swyou1123/ssokdam/Docs/ERD.png

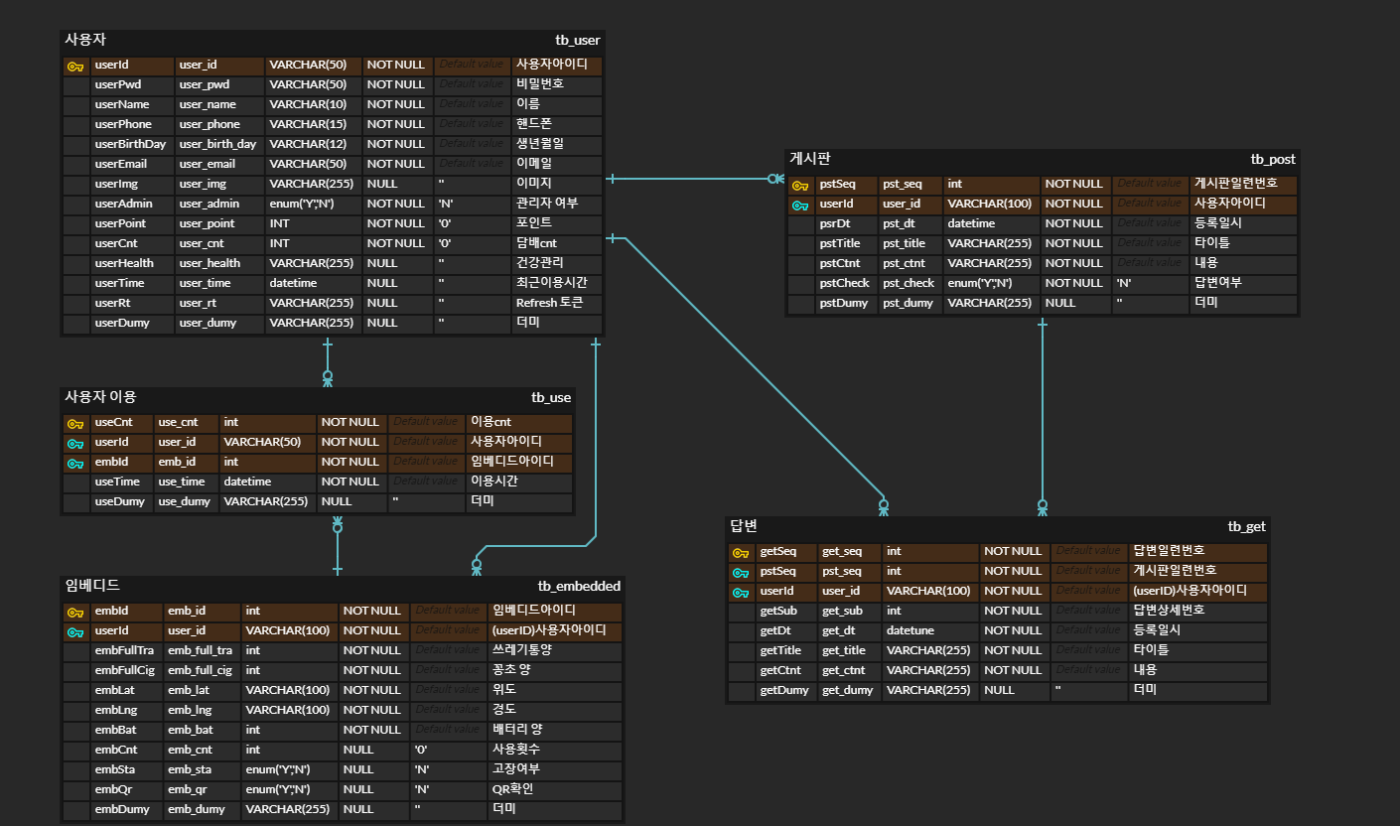
Docs/ERD.png
