swyou1123/ssokdam/Embedded/ESP32s/Sensor/AirQuality_Sensor/Reference/Check.png

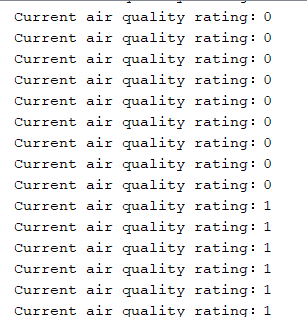
Embedded/ESP32s/Sensor/AirQuality_Sensor/Reference/Check.png
