swyou1123/ssokdam/Embedded/ESP32s/Sensor/Contactfree_Temp_Sensor/Reference/비접촉온도센서 테스트(arduino).png

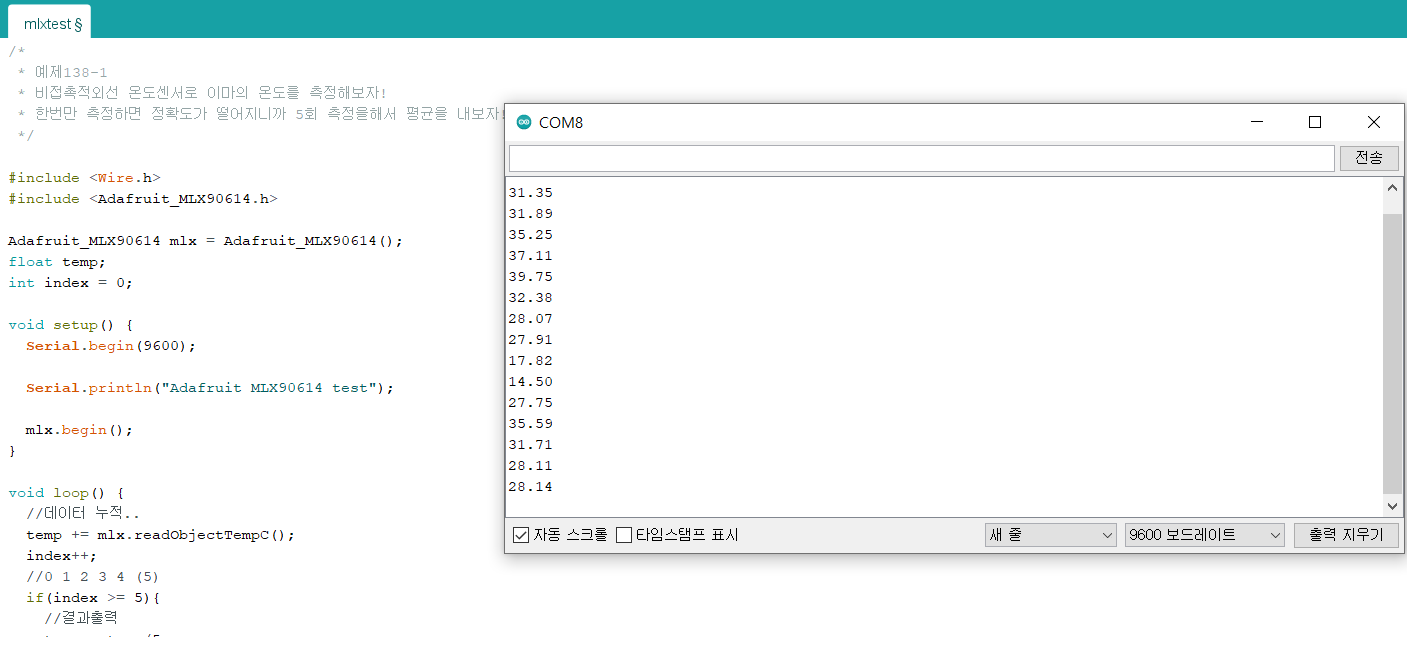
Embedded/ESP32s/Sensor/Contactfree_Temp_Sensor/Reference/비접촉온도센서 테스트(arduino).png
