swyou1123/ssokdam/Embedded/ESP32s/Sensor/GPS_Sensor/Reference/ESP32_GPS.png

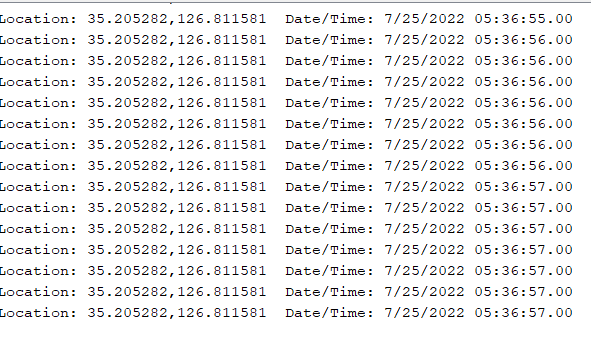
Embedded/ESP32s/Sensor/GPS_Sensor/Reference/ESP32_GPS.png
