swyou1123/ssokdam/Frontend/src/picture/money.png

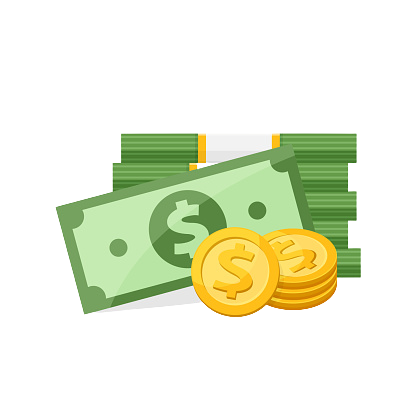
Frontend/src/picture/money.png
