swyou1123/ssokdam/3D_Modelling/Body_2D/Trashbin/Trashbin_Side.SLDPRT

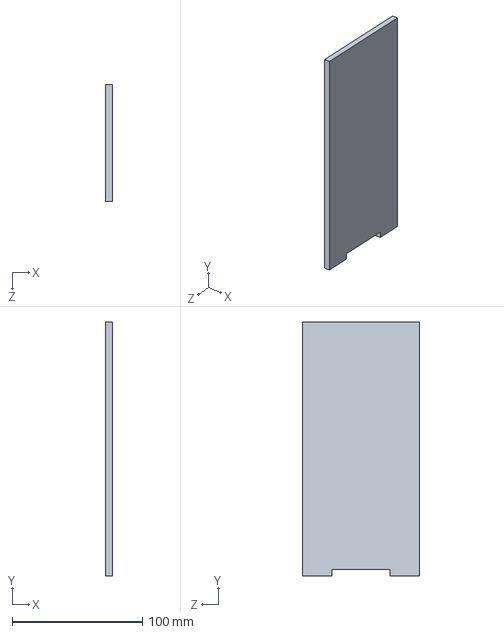
[picture p55: CAD file, 2022-09-26]
3D_Modelling/Body_2D/Trashbin/Trashbin_Side.SLDPRT
5.00 x 195.0 x 89.5 mm
