swyou1123/ssokdam/3D_Modelling/ConnectingRod_2.SLDPRT

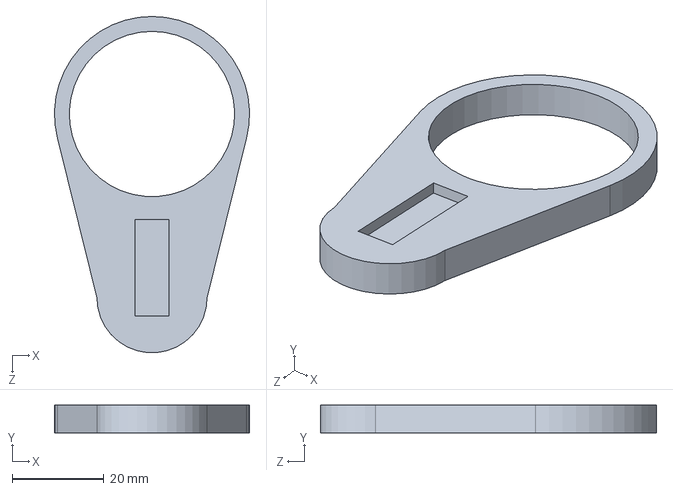
[picture p56: CAD file, 2022-09-26]
3D_Modelling/ConnectingRod_2.SLDPRT
42.5 x 6.00 x 73.2 mm
