swyou1123/ssokdam/3D_Modelling/iris_Mechanism_r0/1.Base.SLDPRT

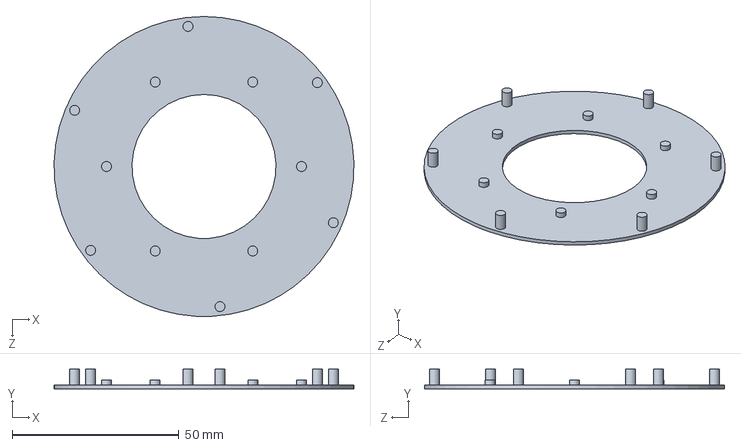
[picture p57: CAD file, 2022-09-26]
3D_Modelling/iris_Mechanism_r0/1.Base.SLDPRT
90.0 x 5.93 x 90.0 mm
