swyou1123/ssokdam/3D_Modelling/iris_Mechanism_r1/1_Base.SLDPRT

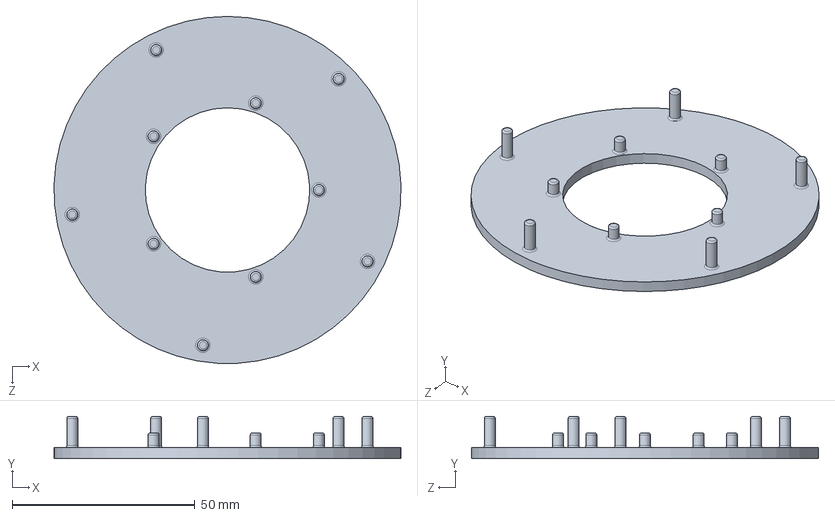
[picture p58: CAD file, 2022-09-26]
3D_Modelling/iris_Mechanism_r1/1_Base.SLDPRT
95.0 x 11.5 x 95.0 mm
