swyou1123/ssokdam/3D_Modelling/Motor/Servo_m.SLDPRT

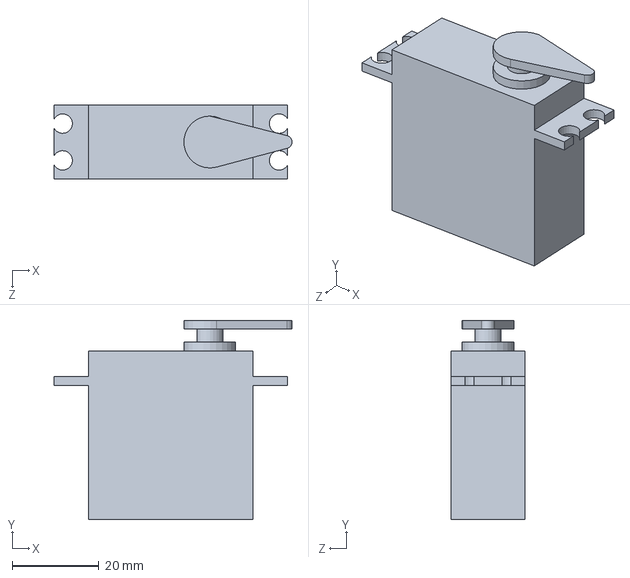
[picture p59: CAD file, 2022-09-26]
3D_Modelling/Motor/Servo_m.SLDPRT
55.0 x 46.0 x 17.0 mm
