swyou1123/ssokdam/3D_Modelling/Printing/Body_Catch.STL

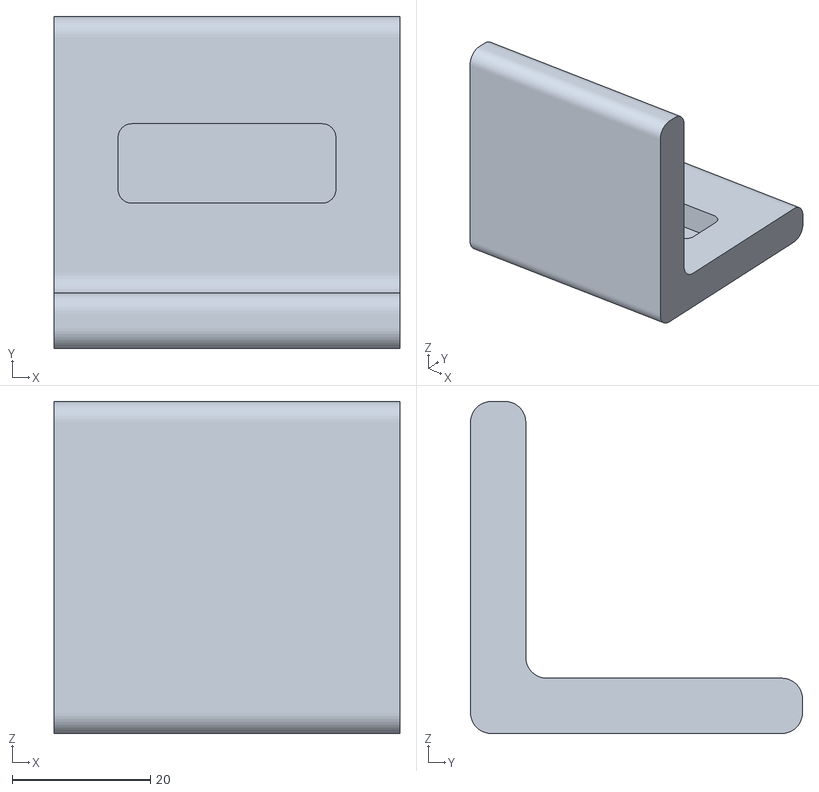
[picture p60: CAD file, 2022-09-26]
3D_Modelling/Printing/Body_Catch.STL
50.0 x 48.0 x 48.0
