swyou1123/ssokdam/3D_Modelling/Printing/Iris_Mech/3_Slider.STL

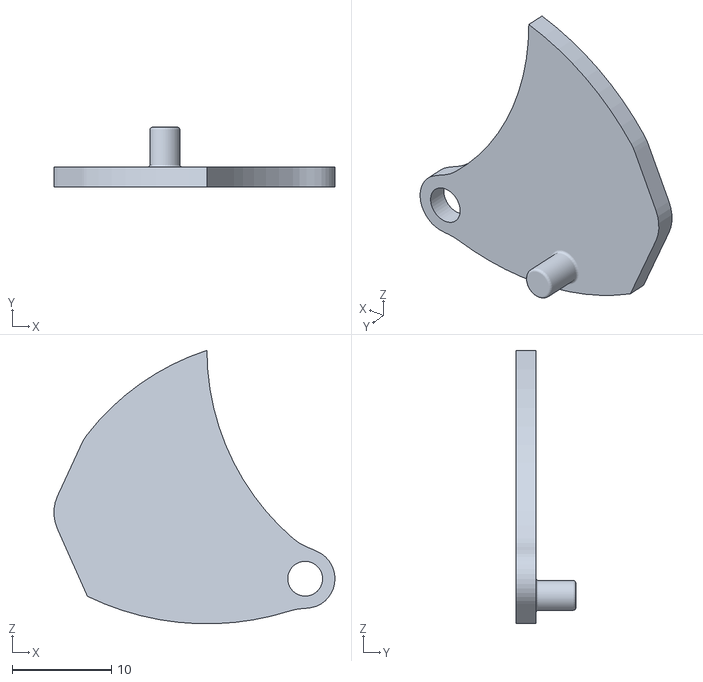
[picture p61: CAD file, 2022-09-26]
3D_Modelling/Printing/Iris_Mech/3_Slider.STL
28.3 x 6.00 x 27.5
