swyou1123/ssokdam/3D_Modelling/Printing/Shedder/Blade.STL

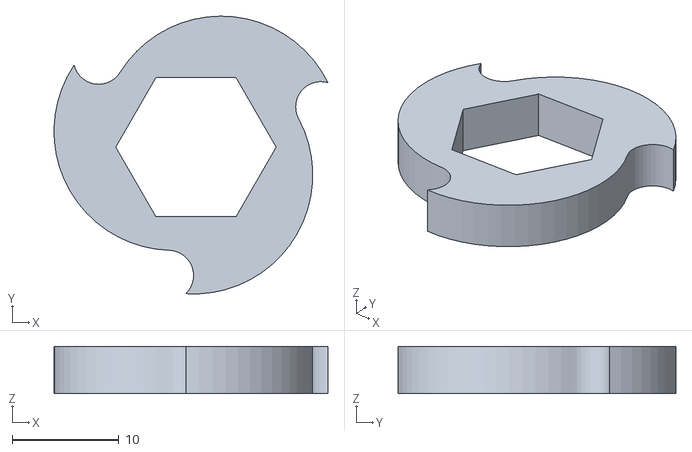
[picture p62: CAD file, 2022-09-26]
3D_Modelling/Printing/Shedder/Blade.STL
25.6 x 26.0 x 4.40
