swyou1123/ssokdam/3D_Modelling/Shedder_Mechanism_r1/Shedder_body.SLDPRT

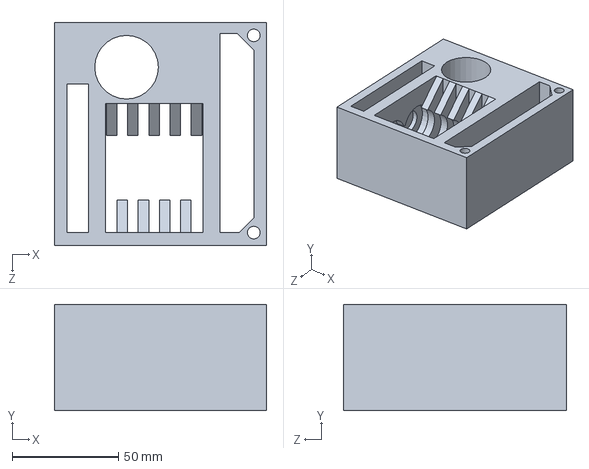
[picture p63: CAD file, 2022-09-26]
3D_Modelling/Shedder_Mechanism_r1/Shedder_body.SLDPRT
100.0 x 50.0 x 105.0 mm
