swyou1123/ssokdam/3D_Modelling/arduino-uno-r3/9. part.SLDPRT

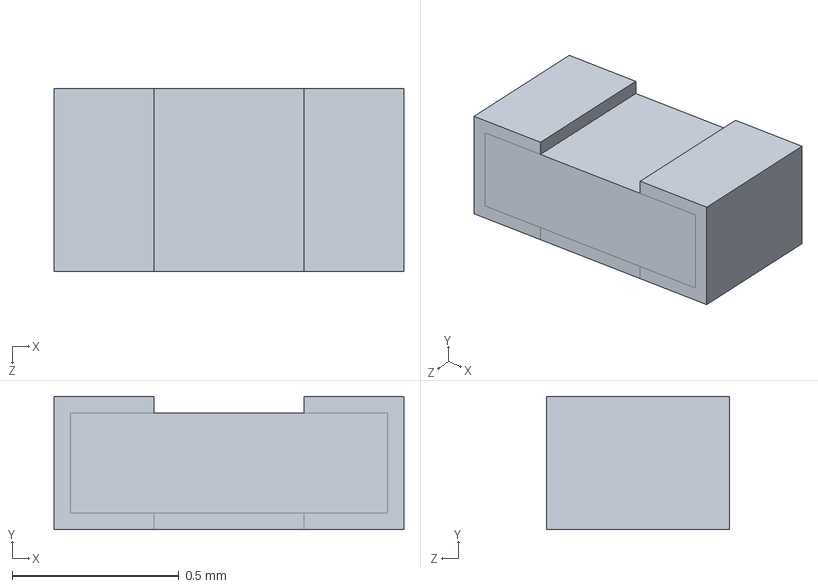
[picture p64: CAD file, 2022-09-26]
3D_Modelling/arduino-uno-r3/9. part.SLDPRT
1.05 x 0.4 x 0.55 mm
