swyou1123/ssokdam/3D_Modelling/arduino-uno-r3/header female/2.0  header female 10.SLDPRT

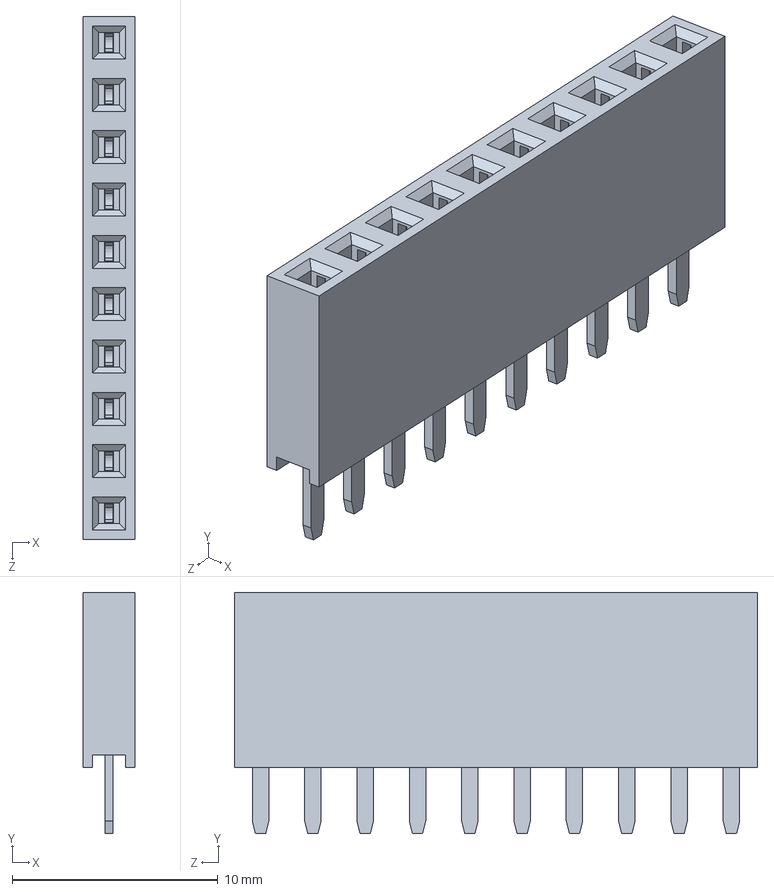
[picture p65: CAD file, 2022-09-26]
3D_Modelling/arduino-uno-r3/header female/2.0 header female 10.SLDPRT
2.54 x 11.7 x 25.4 mm
