swyou1123/ssokdam/3D_Modelling/Body_2D/Body_Temp.SLDPRT

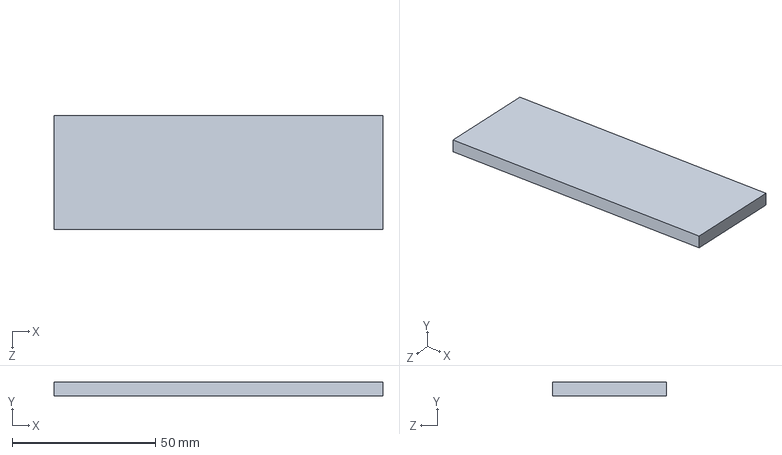
[picture p66: CAD file, 2022-09-26]
3D_Modelling/Body_2D/Body_Temp.SLDPRT
115.0 x 5.00 x 40.0 mm
