swyou1123/ssokdam/3D_Modelling/Body_2D/Trashbin/Trashbin_Bottom.SLDPRT

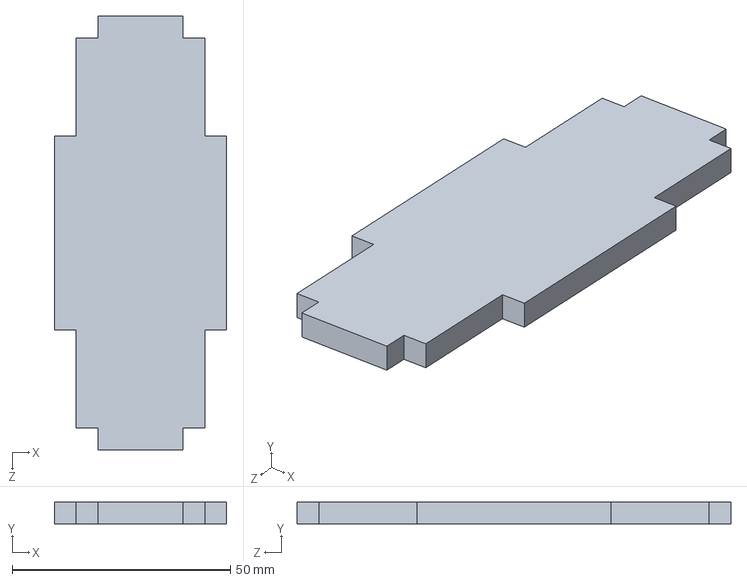
[picture p67: CAD file, 2022-09-26]
3D_Modelling/Body_2D/Trashbin/Trashbin_Bottom.SLDPRT
39.5 x 5.00 x 99.5 mm
