swyou1123/ssokdam/3D_Modelling/iris_Mechanism_r0/6.Pin S.SLDPRT

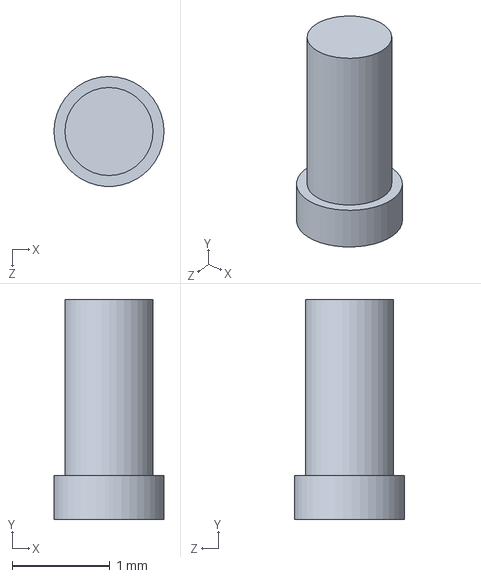
[picture p68: CAD file, 2022-09-26]
3D_Modelling/iris_Mechanism_r0/6.Pin S.SLDPRT
1.12 x 2.25 x 1.12 mm
