swyou1123/ssokdam/3D_Modelling/iris_Mechanism_r1/5_Holder.SLDPRT

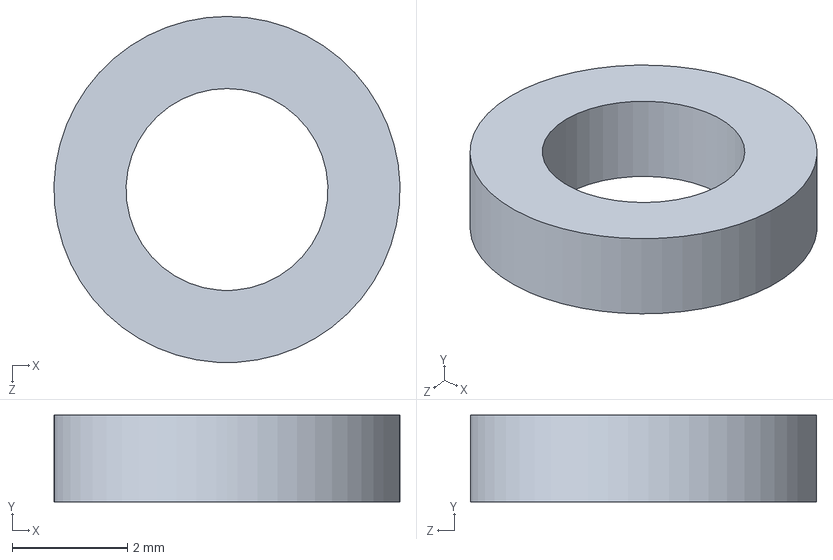
[picture p69: CAD file, 2022-09-26]
3D_Modelling/iris_Mechanism_r1/5_Holder.SLDPRT
6.00 x 1.50 x 6.00 mm
