swyou1123/ssokdam/3D_Modelling/Motor/Servo_s_Wing.SLDPRT

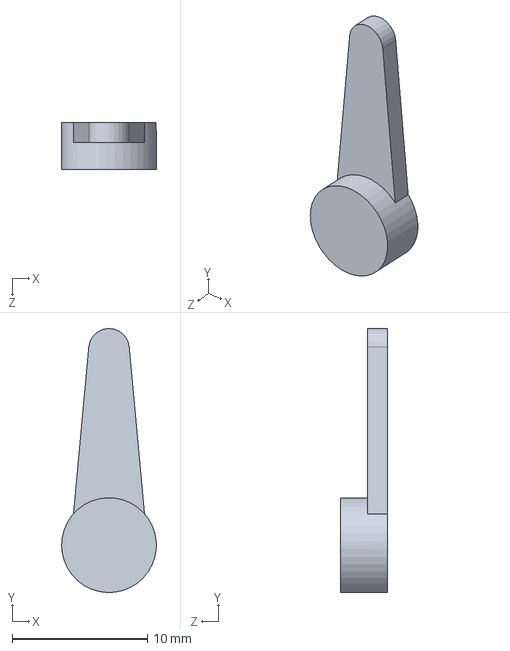
[picture p70: CAD file, 2022-09-26]
3D_Modelling/Motor/Servo_s_Wing.SLDPRT
7.00 x 19.5 x 3.50 mm
