swyou1123/ssokdam/3D_Modelling/Printing/Iris_Mech/2_Ring.STL

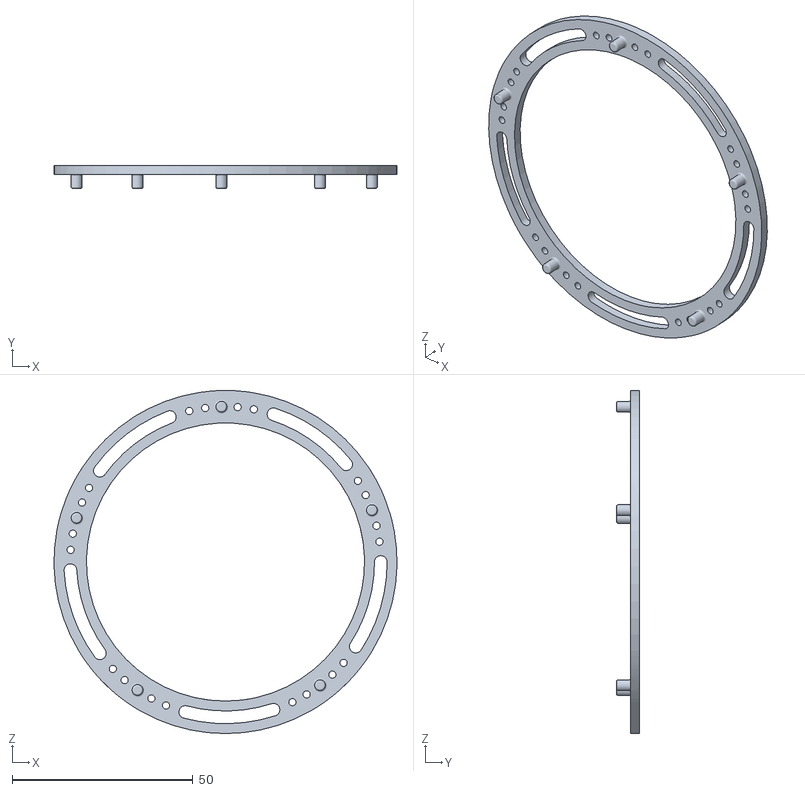
[picture p71: CAD file, 2022-09-26]
3D_Modelling/Printing/Iris_Mech/2_Ring.STL
95.0 x 6.50 x 95.0
