swyou1123/ssokdam/3D_Modelling/Printing/Shedder/Shedder_body_up.STL

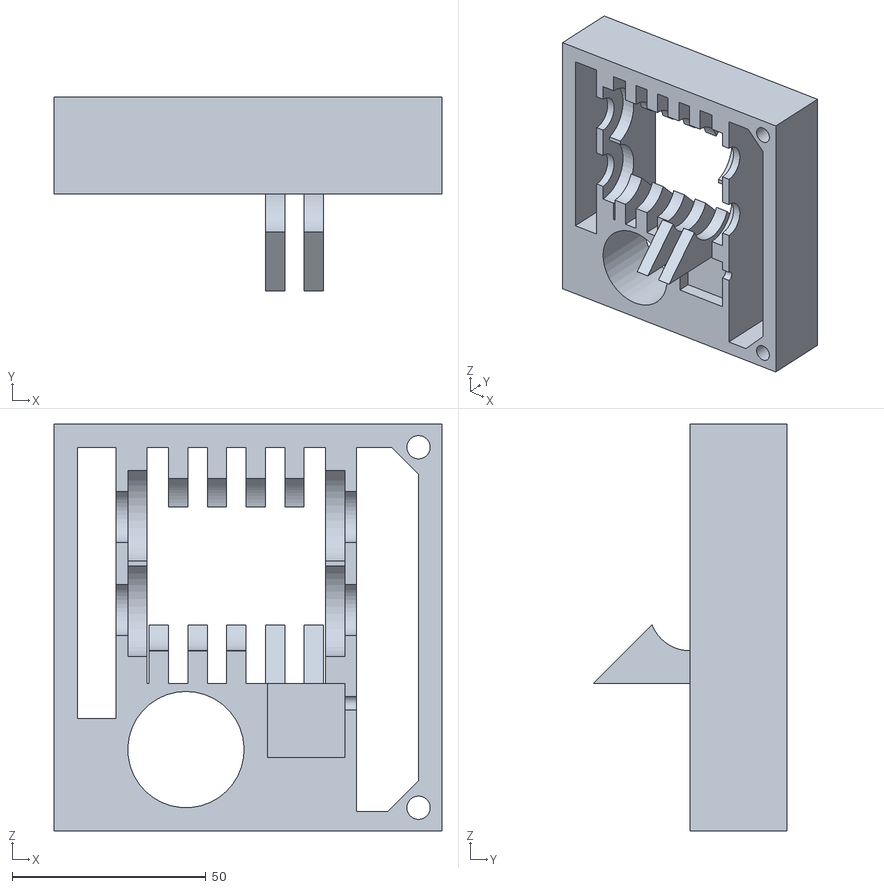
[picture p72: CAD file, 2022-09-26]
3D_Modelling/Printing/Shedder/Shedder_body_up.STL
100.0 x 50.0 x 105.0
