swyou1123/ssokdam/3D_Modelling/Printing/Slider_1.STL

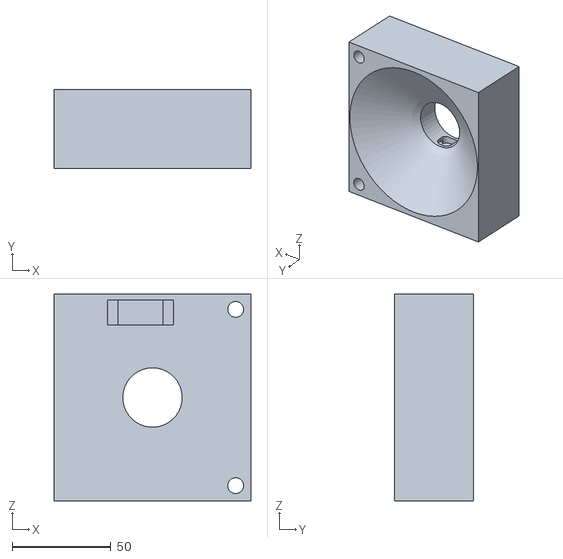
[picture p73: CAD file, 2022-09-26]
3D_Modelling/Printing/Slider_1.STL
99.5 x 40.0 x 104.5
