swyou1123/ssokdam/3D_Modelling/Shedder_Mechanism_r1/Spur_Power_M2Z12.SLDPRT

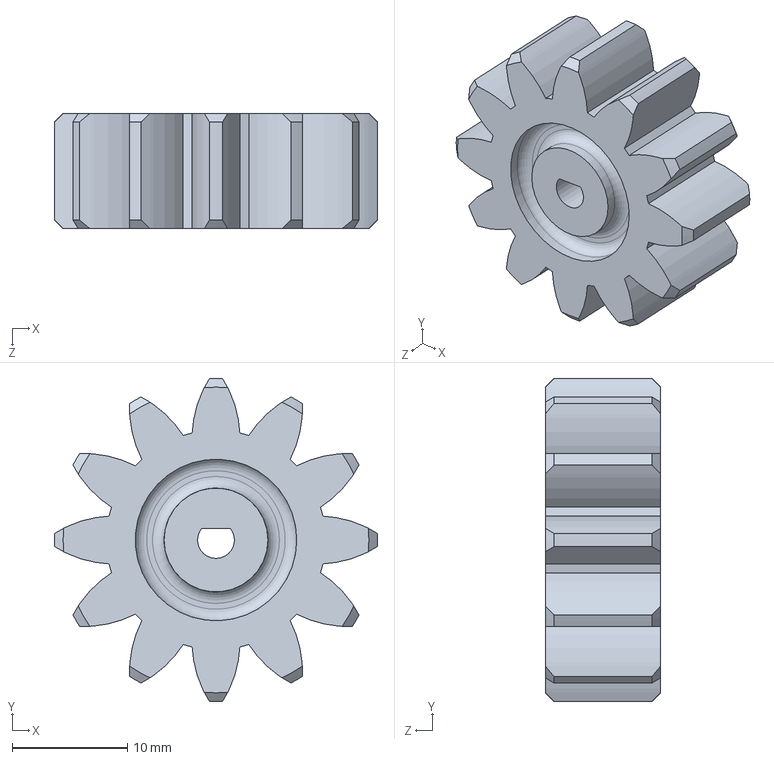
[picture p74: CAD file, 2022-09-26]
3D_Modelling/Shedder_Mechanism_r1/Spur_Power_M2Z12.SLDPRT
28.0 x 28.0 x 10.0 mm
