swyou1123/ssokdam/3D_Modelling/Slider_2.SLDPRT

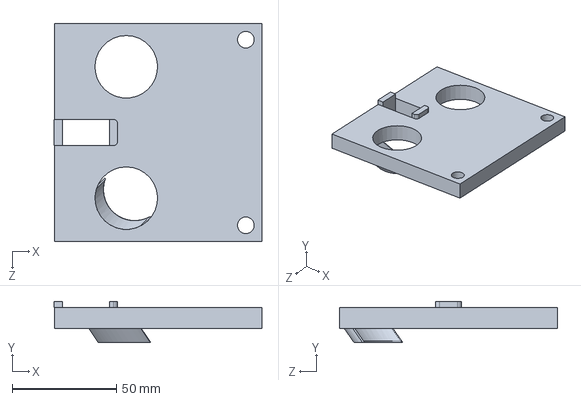
[picture p75: CAD file, 2022-09-26]
3D_Modelling/Slider_2.SLDPRT
99.8 x 19.8 x 104.5 mm
