swyou1123/ssokdam/3D_Modelling/arduino-uno-r3/1. Arduino uno PCB.SLDPRT

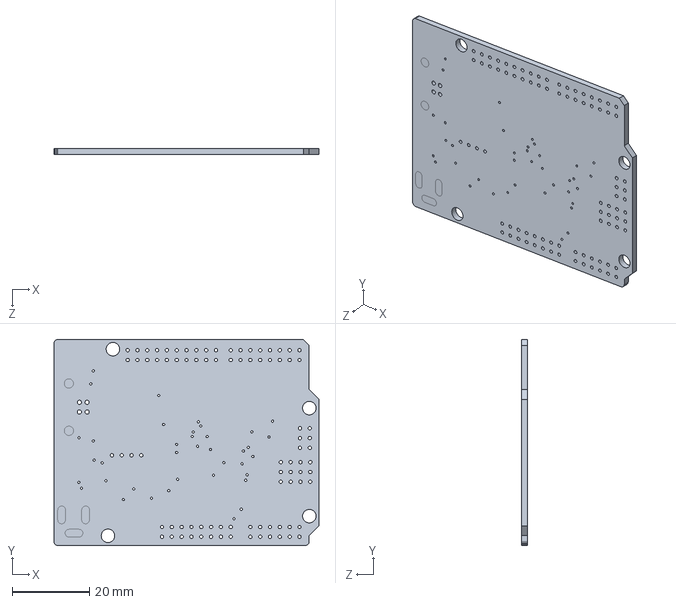
[picture p76: CAD file, 2022-09-26]
3D_Modelling/arduino-uno-r3/1. Arduino uno PCB.SLDPRT
68.5 x 53.3 x 1.60 mm
