swyou1123/ssokdam/3D_Modelling/arduino-uno-r3/header female/1.0 metal.SLDPRT

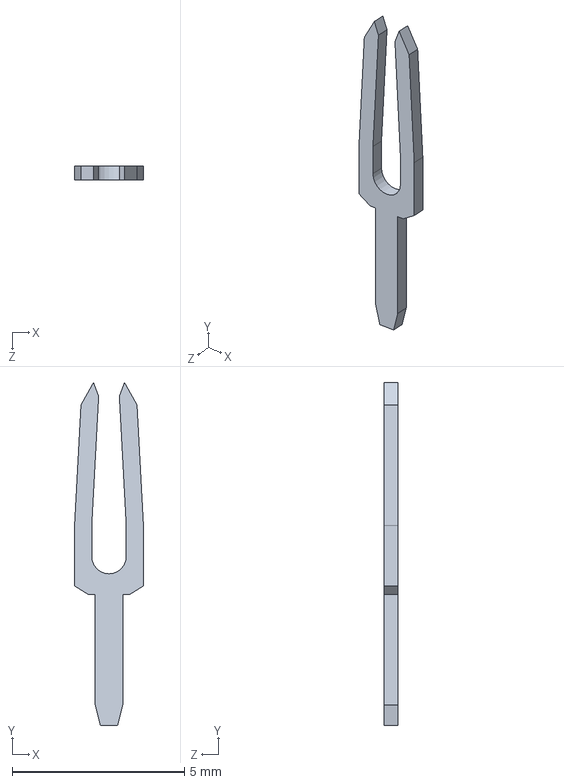
[picture p77: CAD file, 2022-09-26]
3D_Modelling/arduino-uno-r3/header female/1.0 metal.SLDPRT
2.00 x 9.95 x 0.4 mm
