swyou1123/ssokdam/3D_Modelling/Body_2D/Cigbin/Cigbin_Bottom.SLDPRT

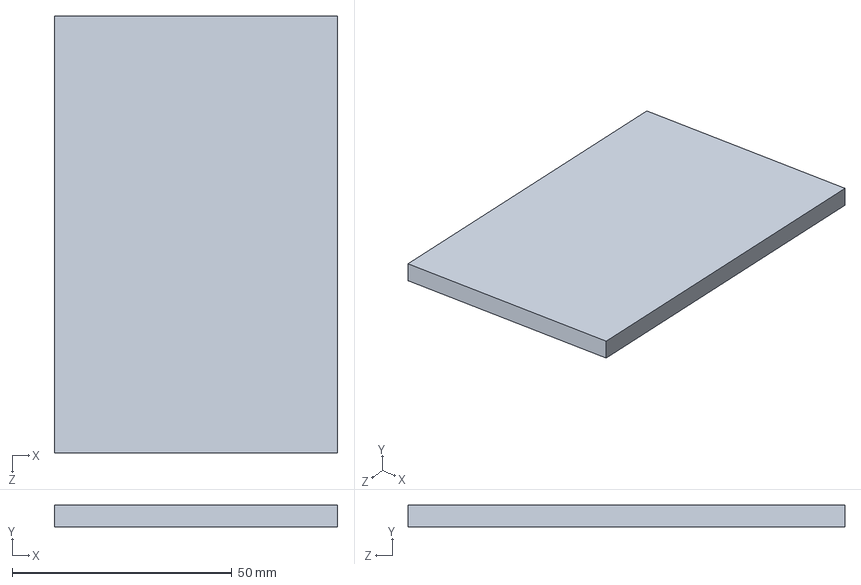
[picture p78: CAD file, 2022-09-26]
3D_Modelling/Body_2D/Cigbin/Cigbin_Bottom.SLDPRT
64.5 x 5.00 x 99.5 mm
