swyou1123/ssokdam/3D_Modelling/iris_Mechanism_r0/2. ring.SLDPRT

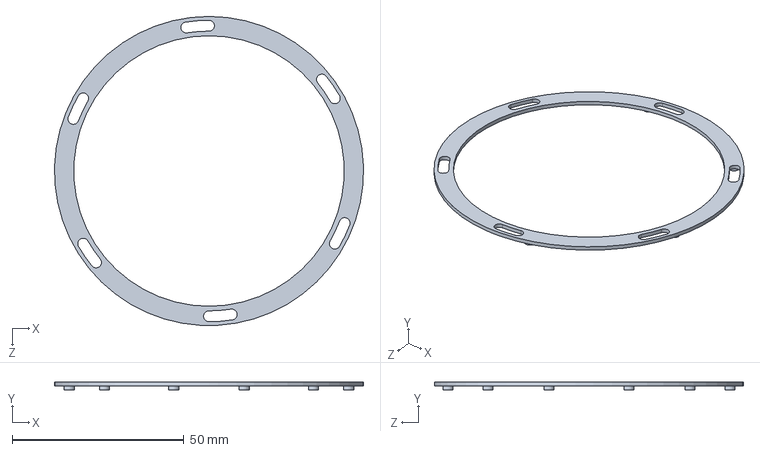
[picture p79: CAD file, 2022-09-26]
3D_Modelling/iris_Mechanism_r0/2. ring.SLDPRT
90.0 x 2.26 x 90.0 mm
