swyou1123/ssokdam/3D_Modelling/iris_Mechanism_r1/4_Link.SLDPRT

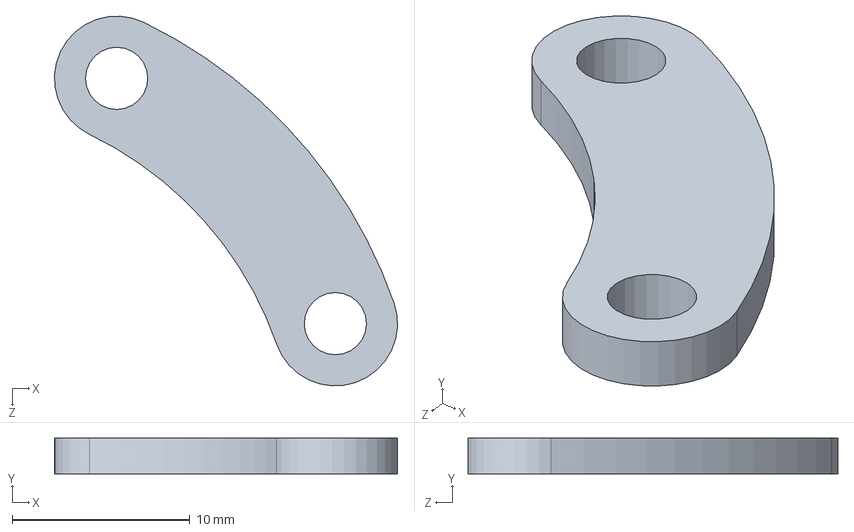
[picture p80: CAD file, 2022-09-26]
3D_Modelling/iris_Mechanism_r1/4_Link.SLDPRT
19.3 x 2.00 x 20.8 mm
