swyou1123/ssokdam/3D_Modelling/Motor/Step_s.SLDPRT

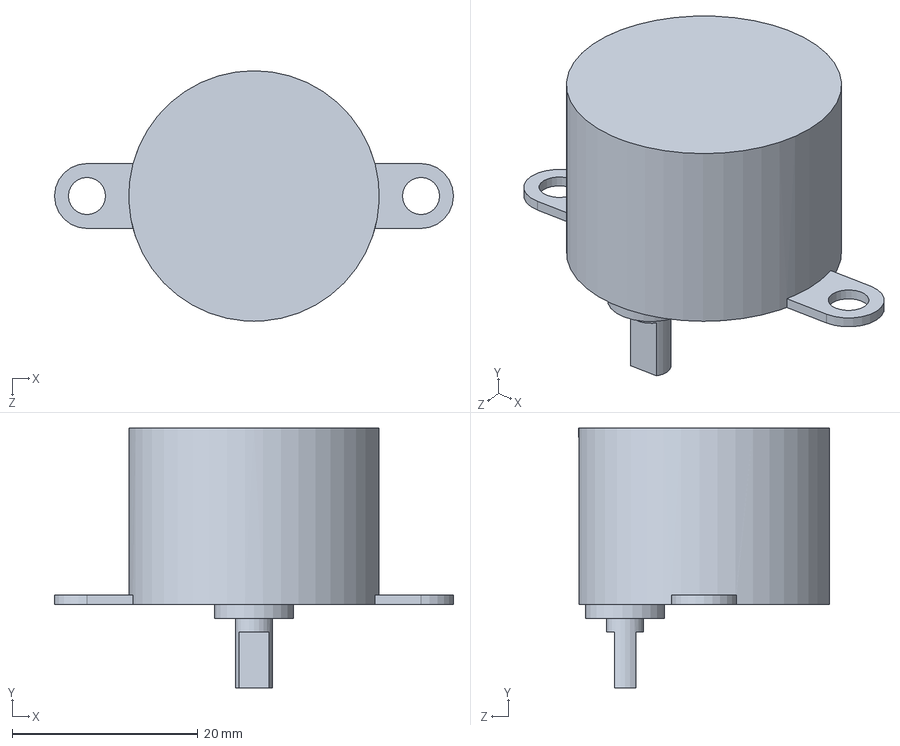
[picture p81: CAD file, 2022-09-26]
3D_Modelling/Motor/Step_s.SLDPRT
43.0 x 28.0 x 27.0 mm
