swyou1123/ssokdam/3D_Modelling/Printing/Shedder/Spacer.STL

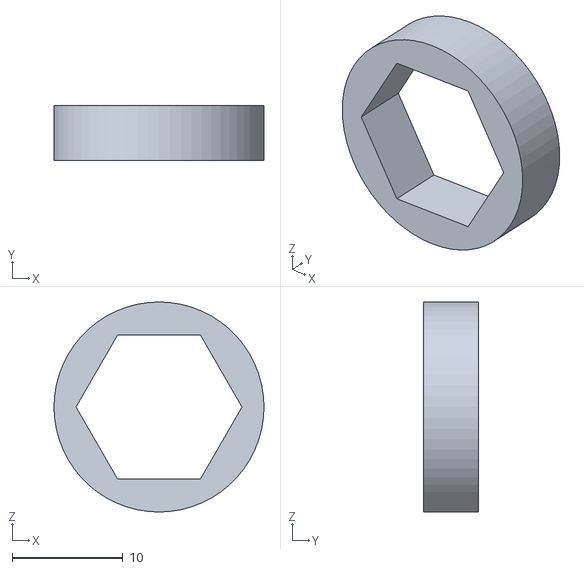
[picture p82: CAD file, 2022-09-26]
3D_Modelling/Printing/Shedder/Spacer.STL
19.0 x 5.00 x 19.0
