swyou1123/ssokdam/3D_Modelling/Ultrasonic_Holder.SLDPRT

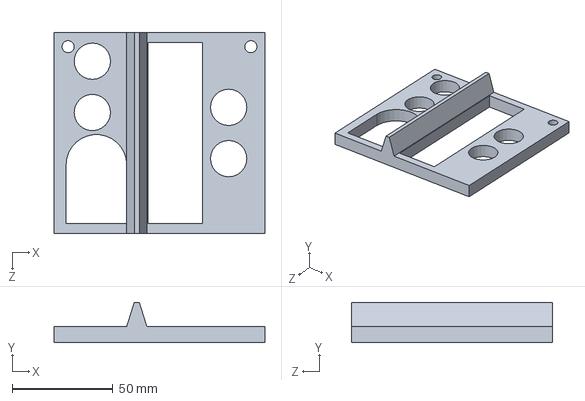
[picture p83: CAD file, 2022-09-26]
3D_Modelling/Ultrasonic_Holder.SLDPRT
104.5 x 20.0 x 99.5 mm
