swyou1123/ssokdam/3D_Modelling/arduino-uno-r3/2. USB.SLDPRT

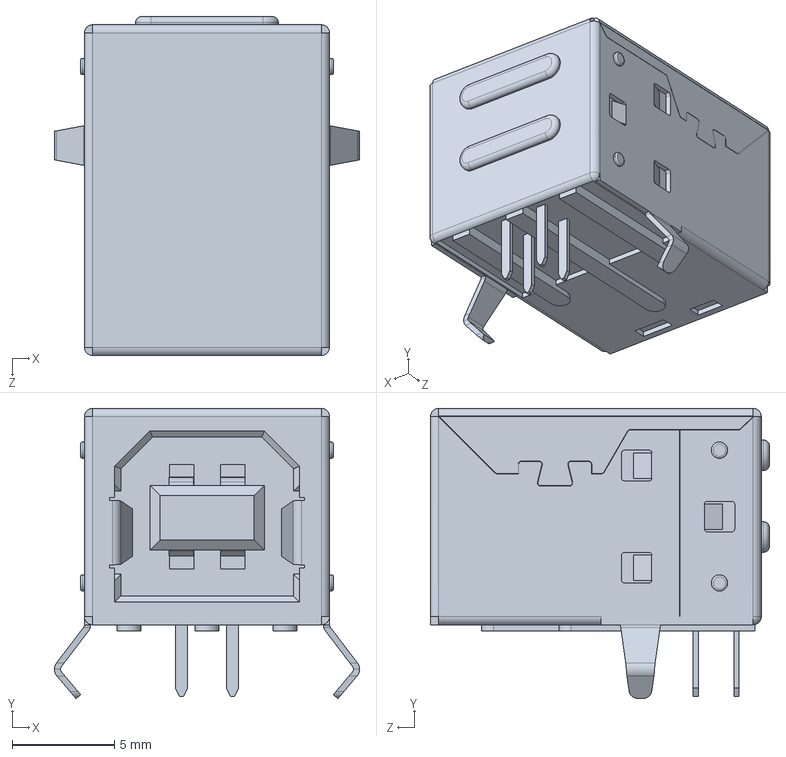
[picture p84: CAD file, 2022-09-26]
3D_Modelling/arduino-uno-r3/2. USB.SLDPRT
14.9 x 14.2 x 16.6 mm
