swyou1123/ssokdam/3D_Modelling/arduino-uno-r3/header female/2.0  header female 6.SLDPRT

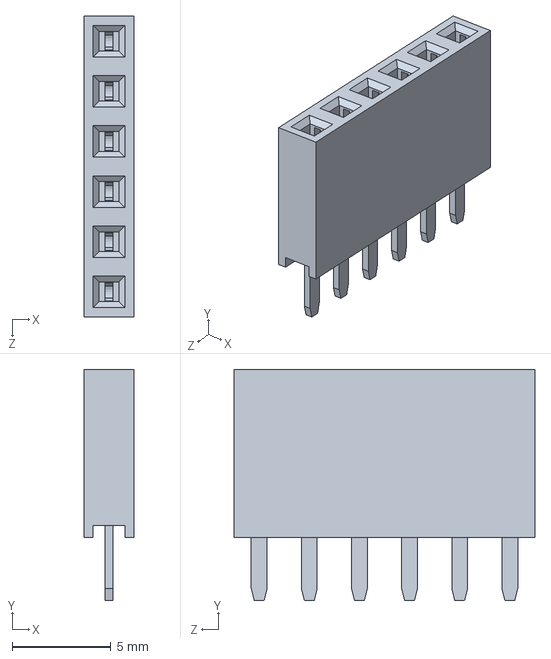
[picture p85: CAD file, 2022-09-26]
3D_Modelling/arduino-uno-r3/header female/2.0 header female 6.SLDPRT
2.54 x 11.7 x 15.2 mm
