swyou1123/ssokdam/3D_Modelling/Body_2D/Body_Front.SLDPRT

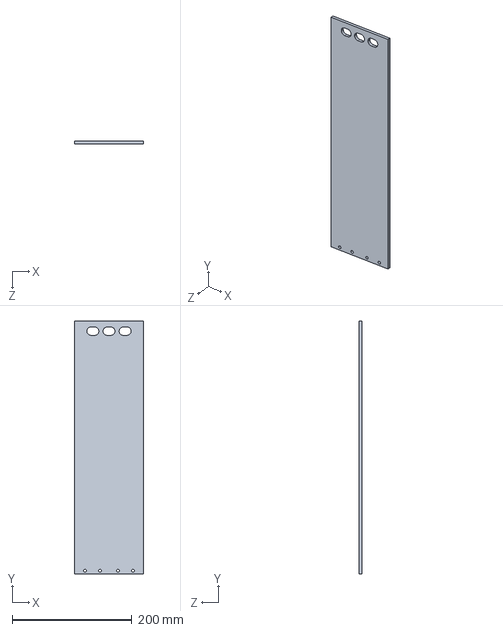
[picture p86: CAD file, 2022-09-26]
3D_Modelling/Body_2D/Body_Front.SLDPRT
115.0 x 423.0 x 5.00 mm
