swyou1123/ssokdam/3D_Modelling/Body_2D/Cigbin/Cigbin_FrontBack.SLDPRT

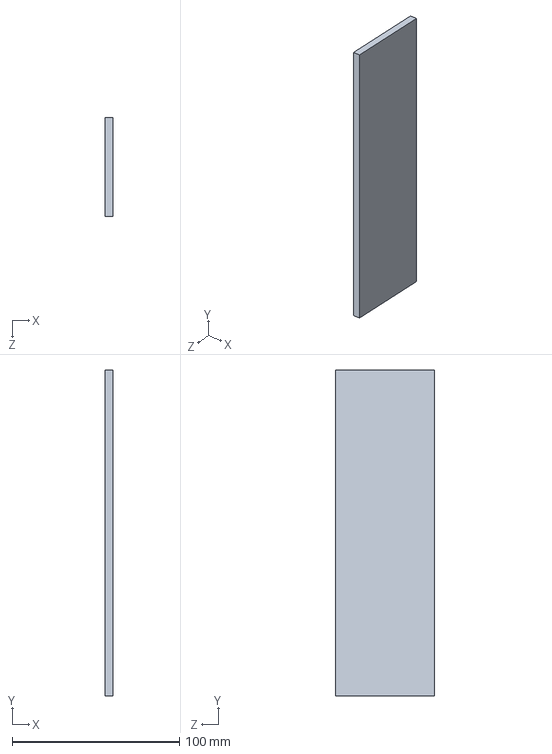
[picture p87: CAD file, 2022-09-26]
3D_Modelling/Body_2D/Cigbin/Cigbin_FrontBack.SLDPRT
5.00 x 195.0 x 59.5 mm
