swyou1123/ssokdam/3D_Modelling/CigbuttBin.SLDPRT

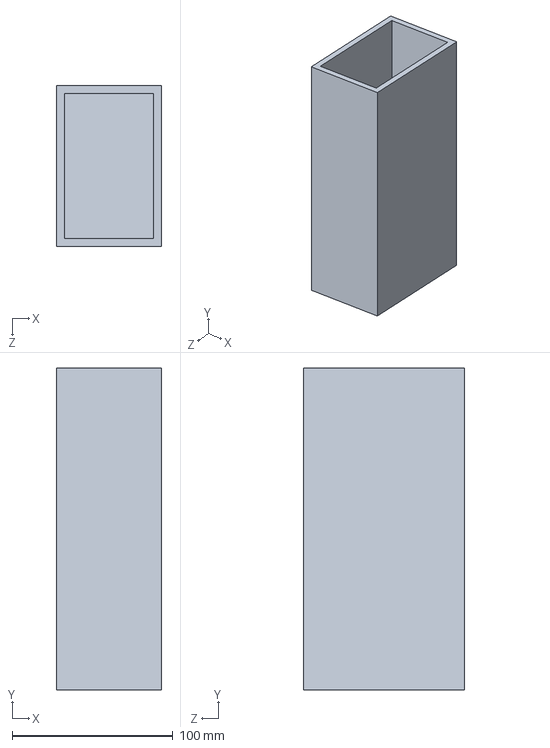
[picture p88: CAD file, 2022-09-26]
3D_Modelling/CigbuttBin.SLDPRT
65.0 x 200.0 x 100.0 mm
