swyou1123/ssokdam/3D_Modelling/Motor/DC.SLDPRT

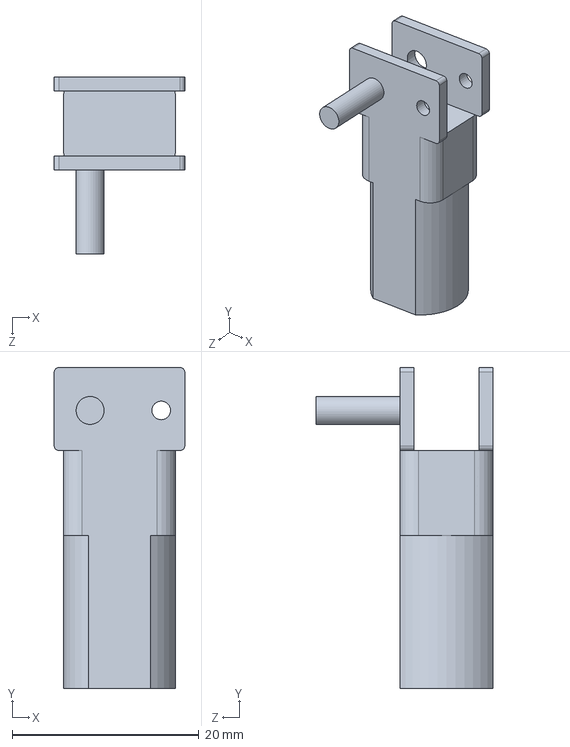
[picture p89: CAD file, 2022-09-26]
3D_Modelling/Motor/DC.SLDPRT
14.0 x 34.4 x 19.0 mm
