swyou1123/ssokdam/3D_Modelling/Printing/Shedder/Shedder_body_down.STL

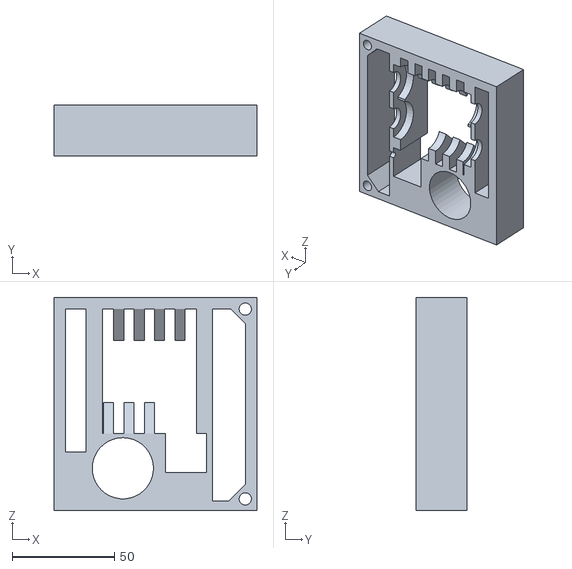
[picture p90: CAD file, 2022-09-26]
3D_Modelling/Printing/Shedder/Shedder_body_down.STL
99.5 x 25.0 x 104.5
