swyou1123/ssokdam/3D_Modelling/Shedder_Mechanism_r1/Shaft.SLDPRT

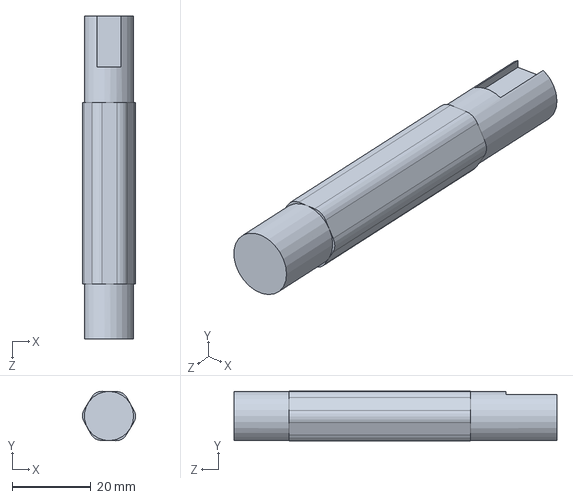
[picture p91: CAD file, 2022-09-26]
3D_Modelling/Shedder_Mechanism_r1/Shaft.SLDPRT
13.5 x 12.6 x 82.0 mm
