swyou1123/ssokdam/3D_Modelling/arduino-uno-r3/7.Lm358 arduino.SLDPRT

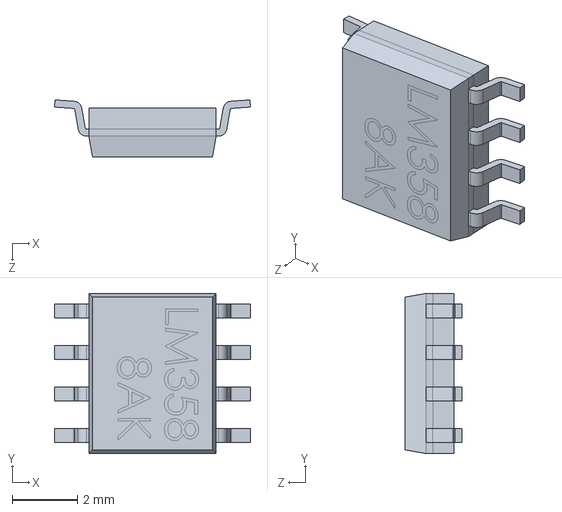
[picture p92: CAD file, 2022-09-26]
3D_Modelling/arduino-uno-r3/7.Lm358 arduino.SLDPRT
6.00 x 4.90 x 1.75 mm
