swyou1123/ssokdam/3D_Modelling/Body_2D/Body_Botton.SLDPRT

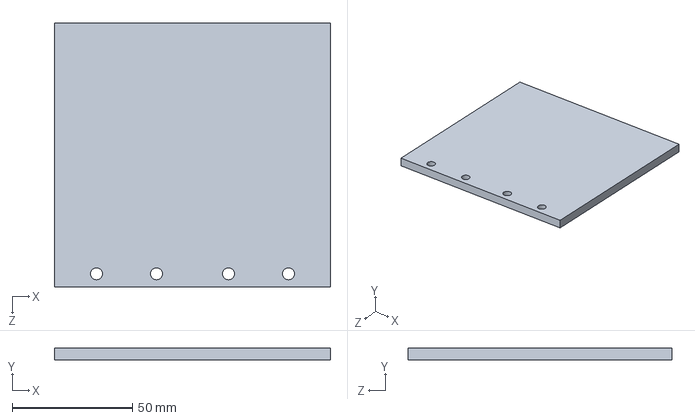
[picture p93: CAD file, 2022-09-26]
3D_Modelling/Body_2D/Body_Botton.SLDPRT
115.0 x 5.00 x 110.0 mm
