swyou1123/ssokdam/3D_Modelling/Body_2D/Trashbin/Trashbin_FrontBack.SLDPRT

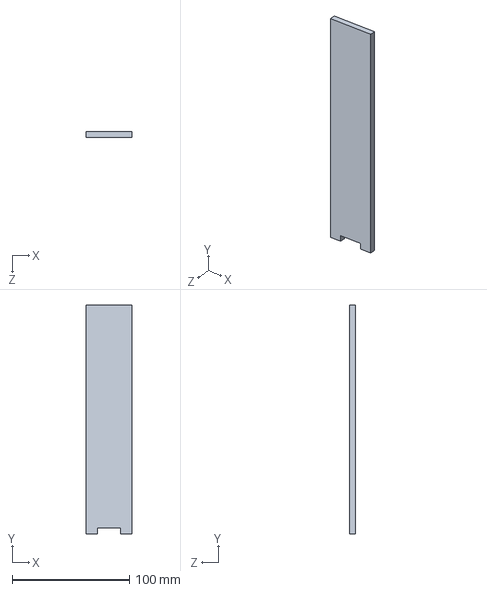
[picture p94: CAD file, 2022-09-26]
3D_Modelling/Body_2D/Trashbin/Trashbin_FrontBack.SLDPRT
39.5 x 195.0 x 5.00 mm
