swyou1123/ssokdam/3D_Modelling/iris_Mechanism_r0/4.Silder balt.SLDPRT

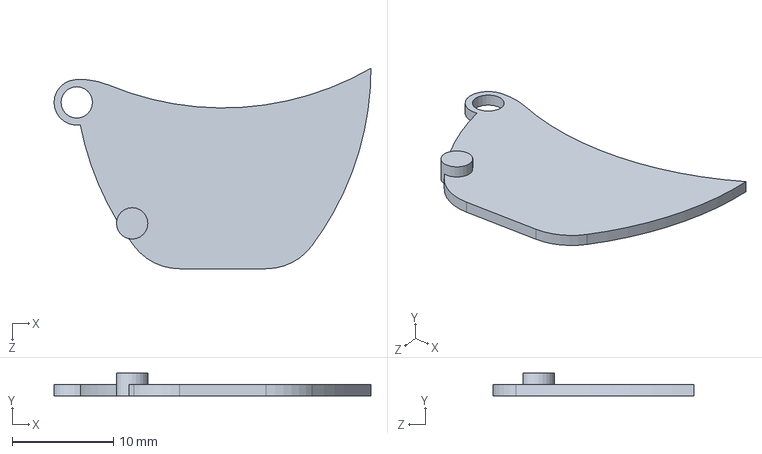
[picture p95: CAD file, 2022-09-26]
3D_Modelling/iris_Mechanism_r0/4.Silder balt.SLDPRT
31.3 x 2.26 x 19.8 mm
