swyou1123/ssokdam/3D_Modelling/Shedder_Mechanism_r1/Bearing_Ring.SLDPRT

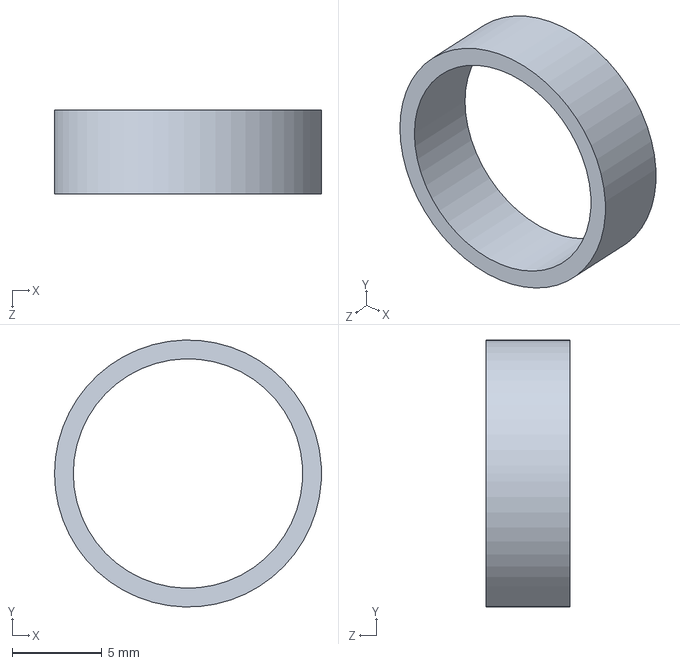
[picture p96: CAD file, 2022-09-26]
3D_Modelling/Shedder_Mechanism_r1/Bearing_Ring.SLDPRT
14.9 x 14.9 x 4.70 mm
