swyou1123/ssokdam/3D_Modelling/Slider_2_Cover.SLDPRT

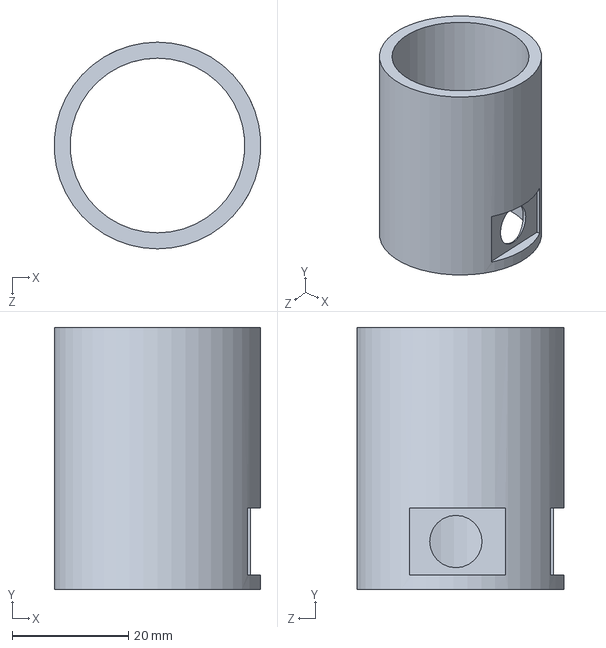
[picture p97: CAD file, 2022-09-26]
3D_Modelling/Slider_2_Cover.SLDPRT
35.4 x 45.0 x 35.5 mm
