swyou1123/ssokdam/3D_Modelling/arduino-uno-r3/3. dc jack arduino.SLDPRT

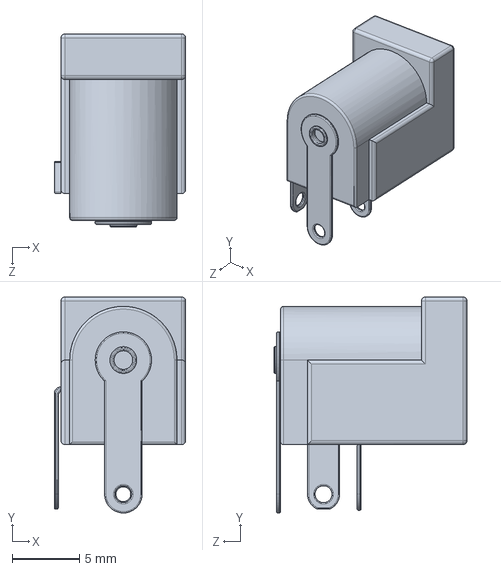
[picture p98: CAD file, 2022-09-26]
3D_Modelling/arduino-uno-r3/3. dc jack arduino.SLDPRT
9.80 x 16.1 x 14.4 mm
