swyou1123/ssokdam/3D_Modelling/iris_Mechanism_r0/5.Pin.SLDPRT

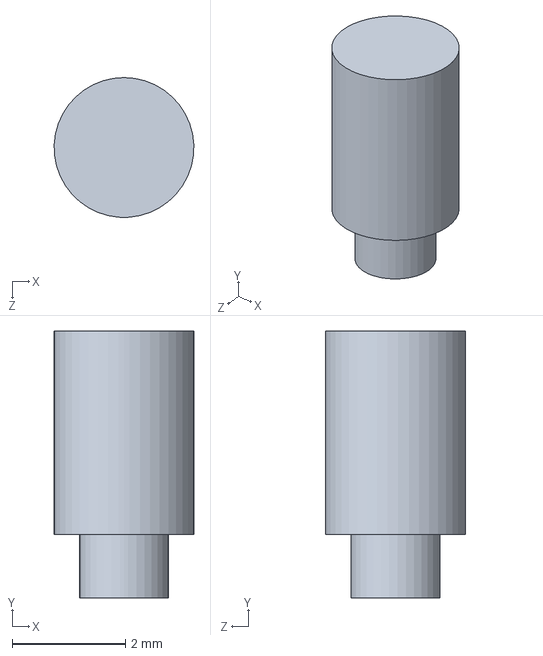
[picture p99: CAD file, 2022-09-26]
3D_Modelling/iris_Mechanism_r0/5.Pin.SLDPRT
2.47 x 4.72 x 2.47 mm
