swyou1123/ssokdam/3D_Modelling/Motor/DC_L.SLDPRT

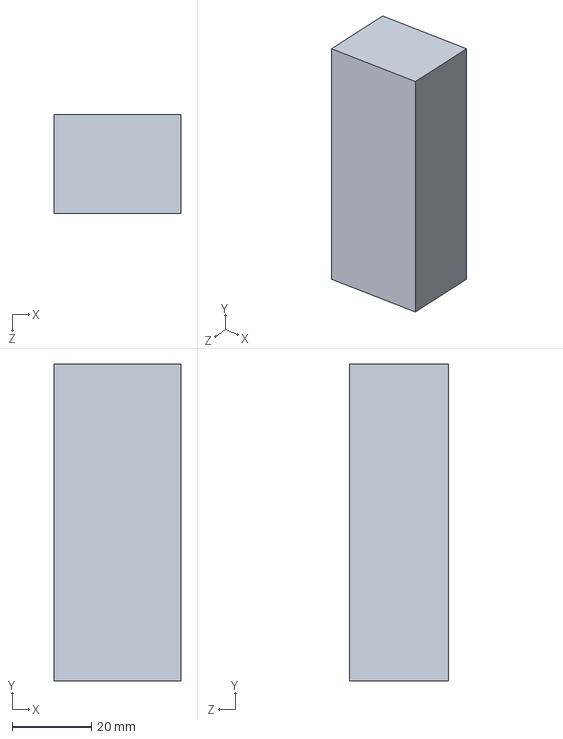
[picture p100: CAD file, 2022-09-26]
3D_Modelling/Motor/DC_L.SLDPRT
32.0 x 80.0 x 25.0 mm
