swyou1123/ssokdam/3D_Modelling/NeoPixel.SLDPRT

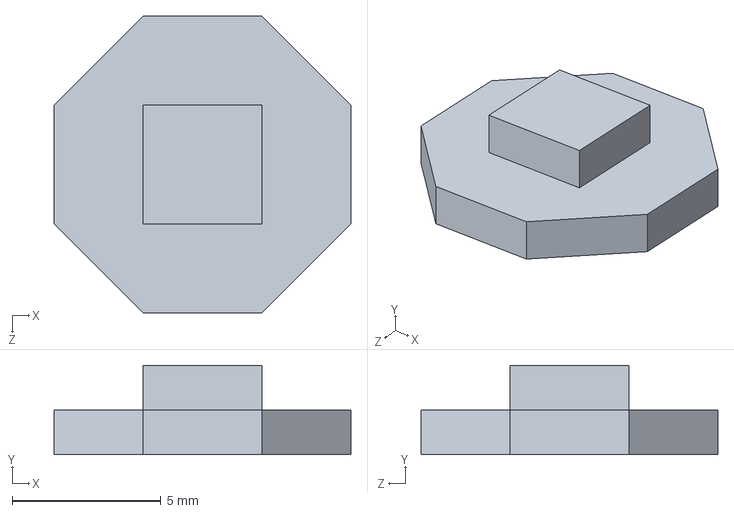
[picture p101: CAD file, 2022-09-26]
3D_Modelling/NeoPixel.SLDPRT
10.0 x 3.00 x 10.0 mm
