swyou1123/ssokdam/3D_Modelling/Printing/Shedder/Spur_Trans_M2Z24.STL

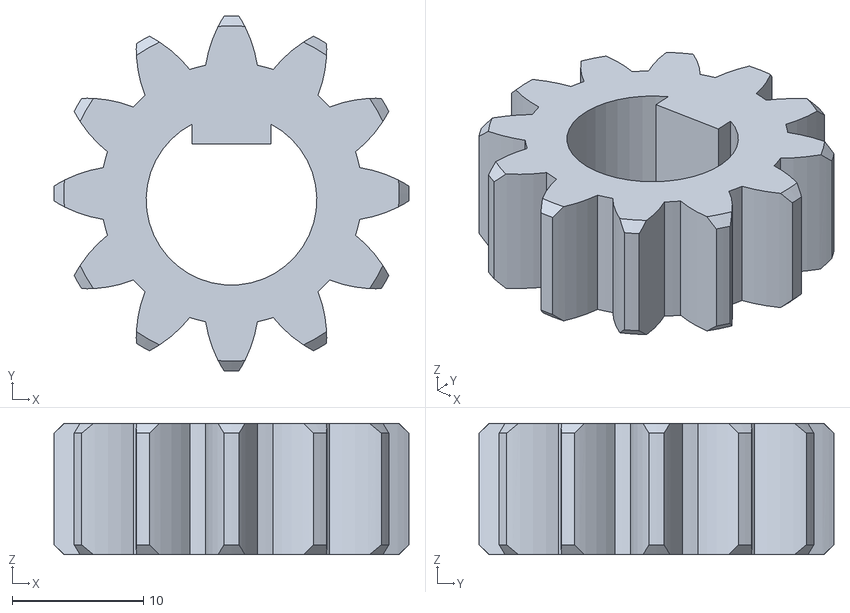
[picture p102: CAD file, 2022-09-26]
3D_Modelling/Printing/Shedder/Spur_Trans_M2Z24.STL
27.0 x 27.0 x 10.0
