swyou1123/ssokdam/3D_Modelling/Shedder_Mechanism_r1/Shedder_cover.SLDPRT

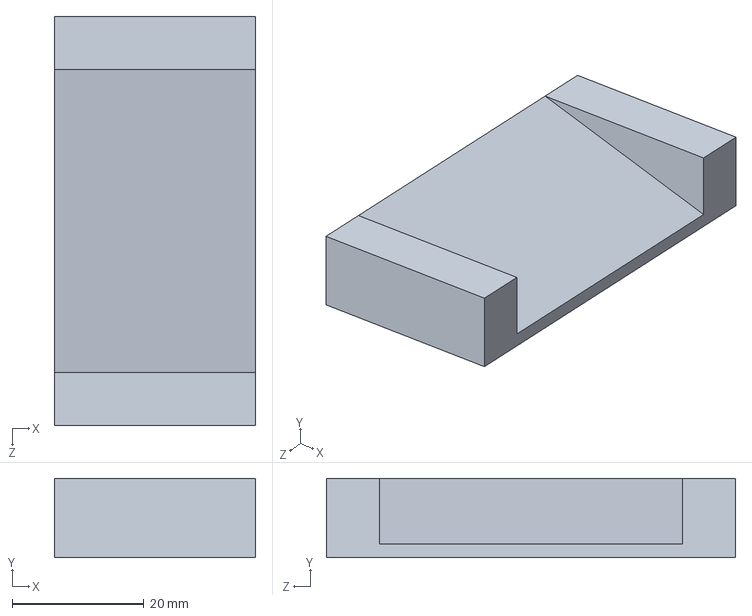
[picture p103: CAD file, 2022-09-26]
3D_Modelling/Shedder_Mechanism_r1/Shedder_cover.SLDPRT
30.5 x 12.0 x 62.0 mm
