swyou1123/ssokdam/3D_Modelling/arduino-uno-r3/5. header male.SLDPRT

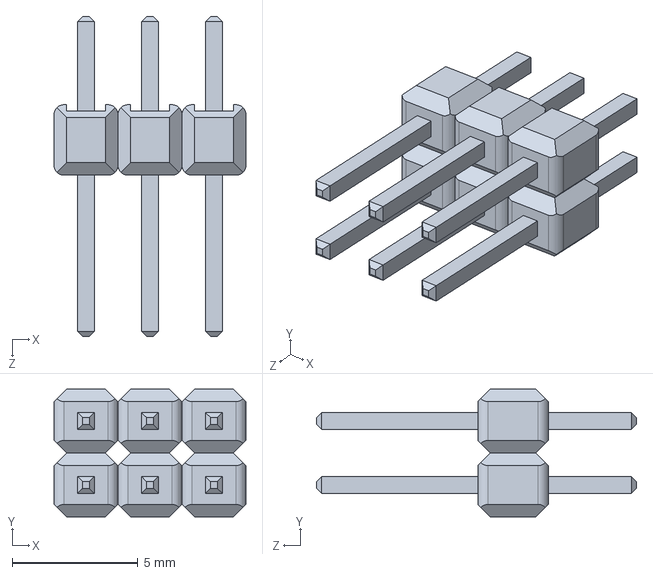
[picture p104: CAD file, 2022-09-26]
3D_Modelling/arduino-uno-r3/5. header male.SLDPRT
7.62 x 5.08 x 12.7 mm
