swyou1123/ssokdam/3D_Modelling/Body_2D/Body_Top.SLDPRT

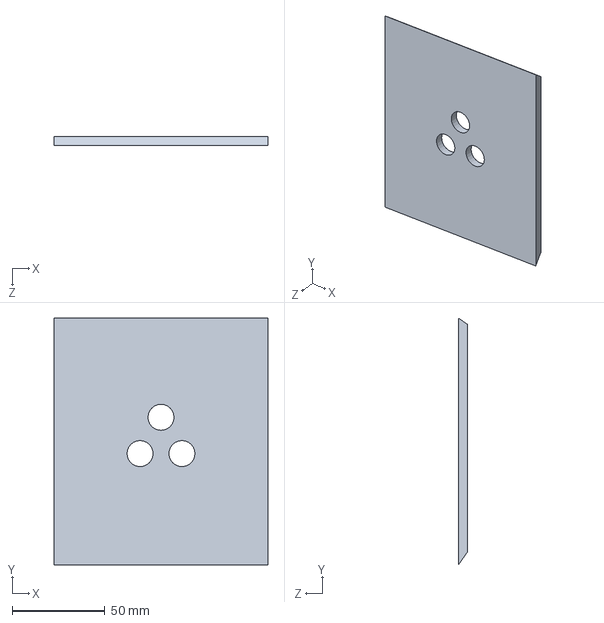
[picture p105: CAD file, 2022-09-26]
3D_Modelling/Body_2D/Body_Top.SLDPRT
115.0 x 132.8 x 5.00 mm
