swyou1123/ssokdam/3D_Modelling/iris_Mechanism_r0/3.balt.SLDPRT

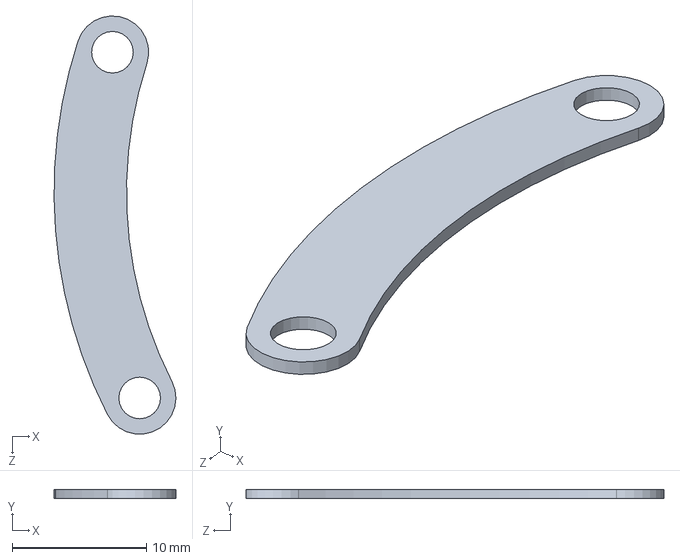
[picture p106: CAD file, 2022-09-26]
3D_Modelling/iris_Mechanism_r0/3.balt.SLDPRT
9.08 x 0.675 x 31.1 mm
