swyou1123/ssokdam/3D_Modelling/Motor/Servo_s_Body.SLDPRT

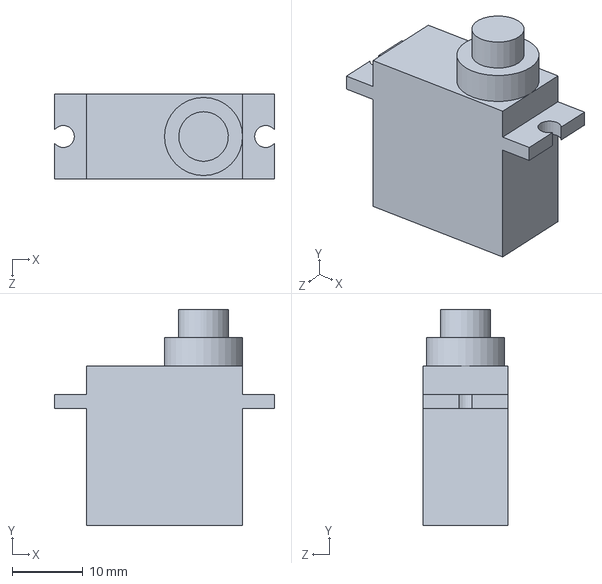
[picture p107: CAD file, 2022-09-26]
3D_Modelling/Motor/Servo_s_Body.SLDPRT
31.0 x 30.5 x 12.0 mm
