swyou1123/ssokdam/3D_Modelling/TrashBin.SLDPRT

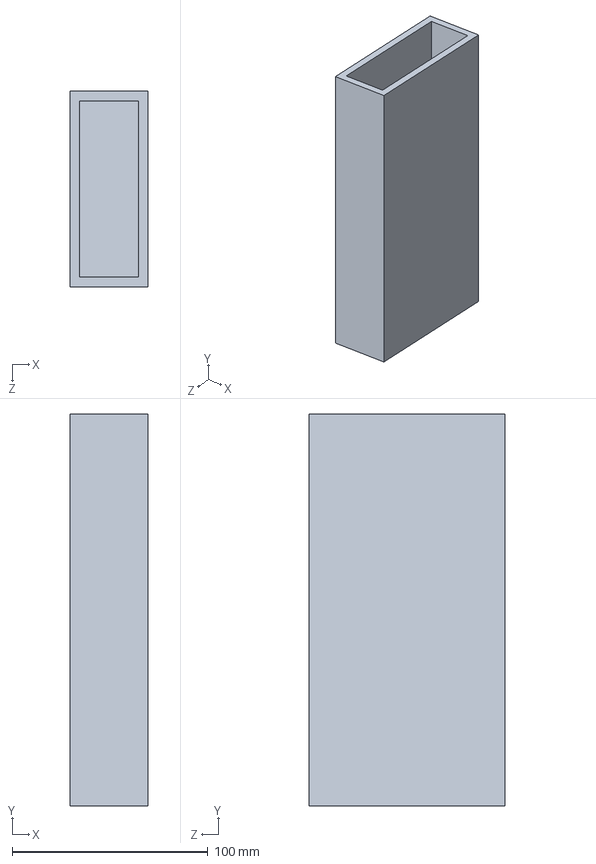
[picture p108: CAD file, 2022-09-26]
3D_Modelling/TrashBin.SLDPRT
40.0 x 200.0 x 100.0 mm
