swyou1123/ssokdam/3D_Modelling/arduino-uno-r3/6. diode.SLDPRT

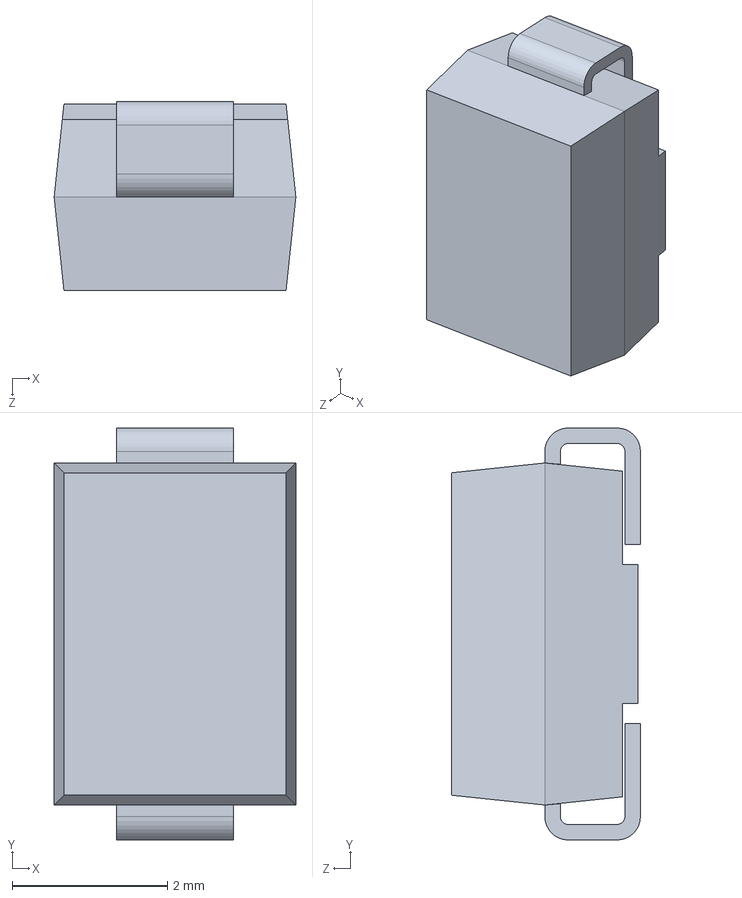
[picture p109: CAD file, 2022-09-26]
3D_Modelling/arduino-uno-r3/6. diode.SLDPRT
3.11 x 5.30 x 2.43 mm
