swyou1123/ssokdam/3D_Modelling/Body.SLDPRT

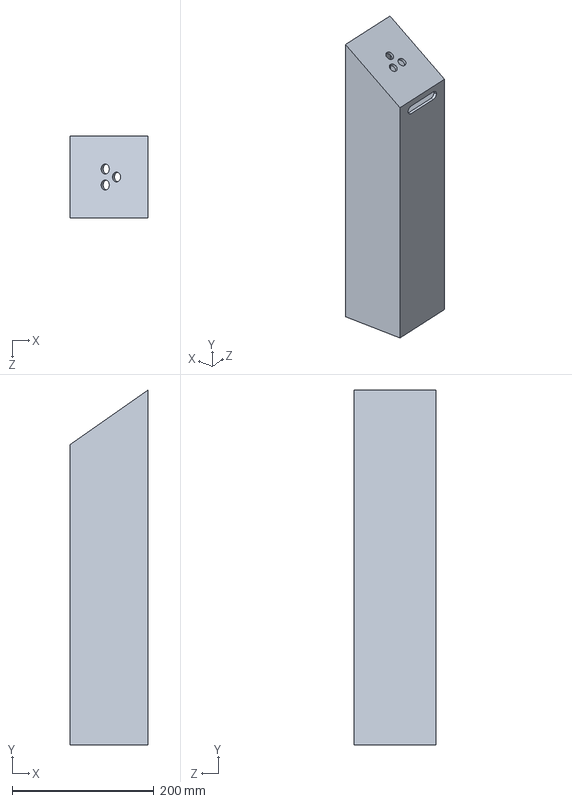
[picture p110: CAD file, 2022-09-26]
3D_Modelling/Body.SLDPRT
110.0 x 500.0 x 115.0 mm
