swyou1123/ssokdam/3D_Modelling/Body_2D/Body_Side.SLDPRT

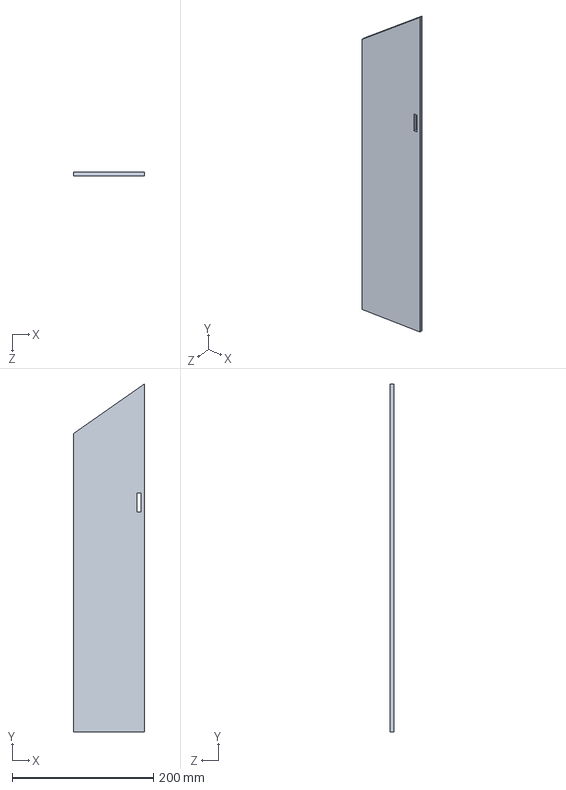
[picture p111: CAD file, 2022-09-26]
3D_Modelling/Body_2D/Body_Side.SLDPRT
100.0 x 493.0 x 5.00 mm
