swyou1123/ssokdam/3D_Modelling/arduino-uno-r3/4. atmega 328p.SLDPRT

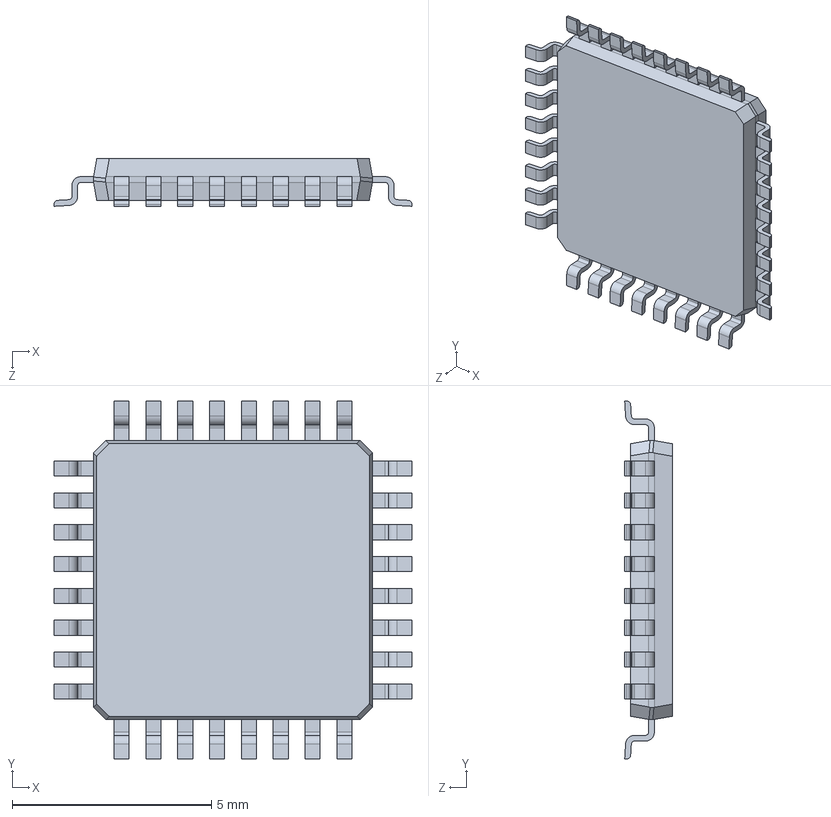
[picture p112: CAD file, 2022-09-26]
3D_Modelling/arduino-uno-r3/4. atmega 328p.SLDPRT
8.99 x 8.99 x 1.20 mm
