swyou1123/ssokdam/3D_Modelling/ConnectingRod_1.SLDPRT

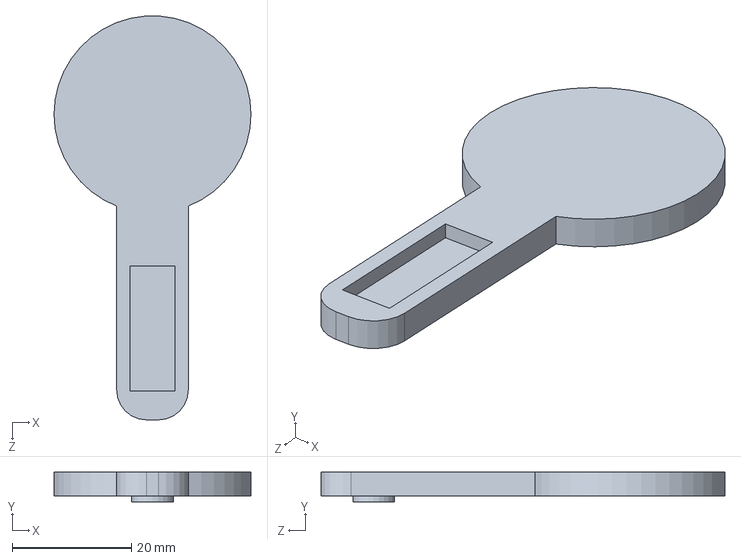
[picture p113: CAD file, 2022-09-26]
3D_Modelling/ConnectingRod_1.SLDPRT
33.0 x 5.00 x 67.6 mm
