swyou1123/ssokdam/3D_Modelling/Shedder_Mechanism_r1/Bearing.SLDPRT

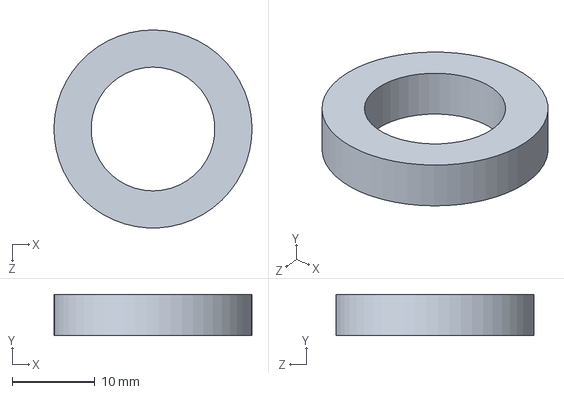
[picture p114: CAD file, 2022-09-26]
3D_Modelling/Shedder_Mechanism_r1/Bearing.SLDPRT
24.0 x 5.00 x 24.0 mm
