swyou1123/ssokdam/3D_Modelling/arduino-uno-r3/13. LM1117.SLDPRT

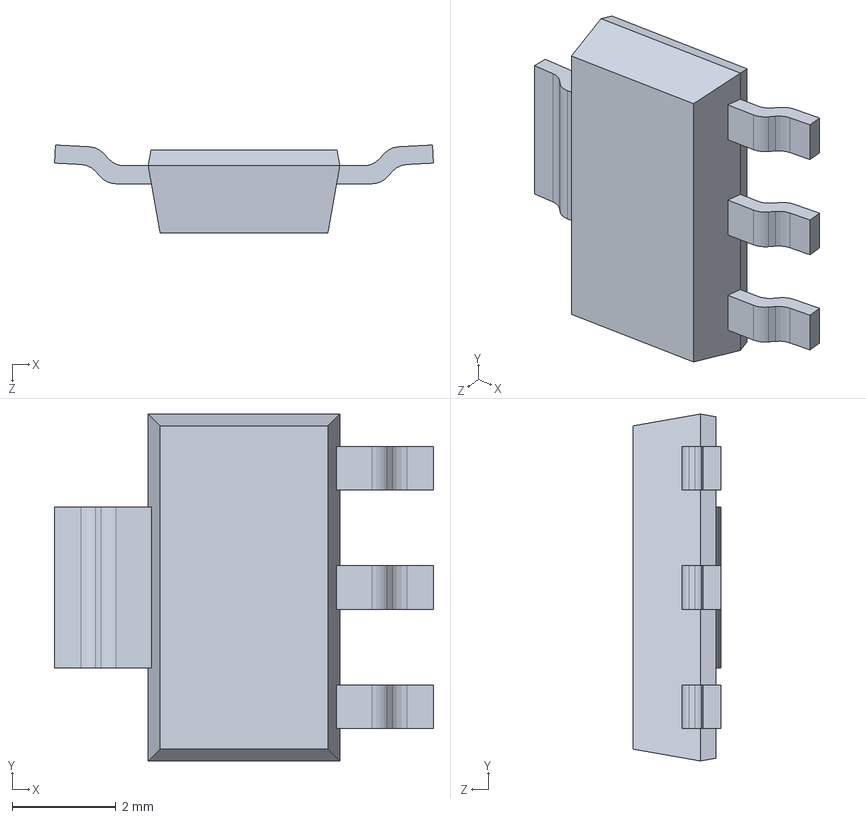
[picture p115: CAD file, 2022-09-26]
3D_Modelling/arduino-uno-r3/13. LM1117.SLDPRT
7.32 x 6.70 x 1.70 mm
