swyou1123/ssokdam/3D_Modelling/Battery_Pack.SLDPRT

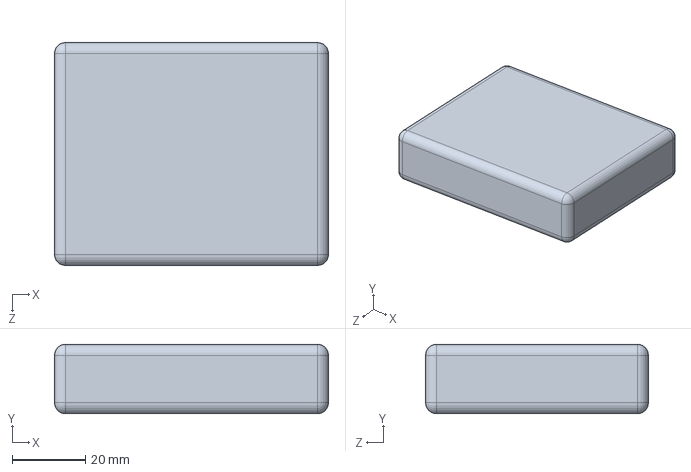
[picture p116: CAD file, 2022-09-26]
3D_Modelling/Battery_Pack.SLDPRT
75.0 x 19.0 x 61.0 mm
