swyou1123/ssokdam/3D_Modelling/arduino-uno-r3/15. part 1.SLDPRT

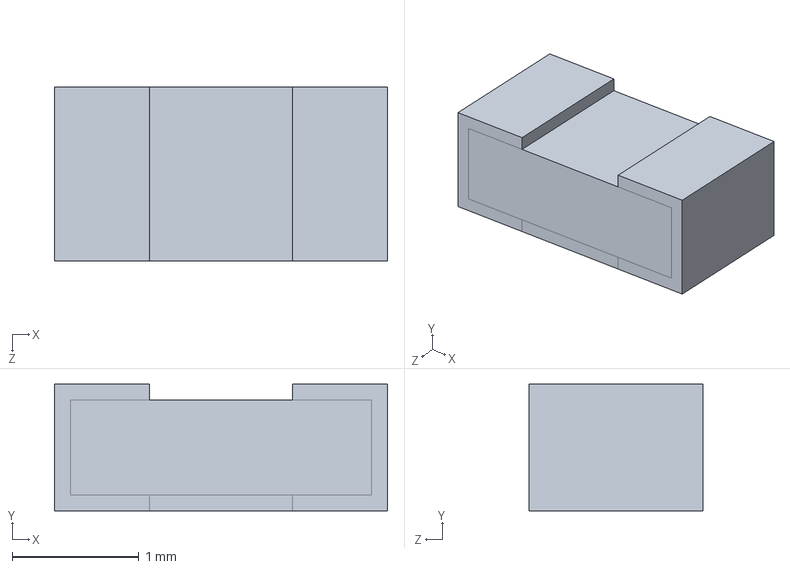
[picture p117: CAD file, 2022-09-26]
3D_Modelling/arduino-uno-r3/15. part 1.SLDPRT
2.62 x 1.00 x 1.38 mm
