swyou1123/ssokdam/3D_Modelling/arduino-uno-r3/12. Button arduino.SLDPRT

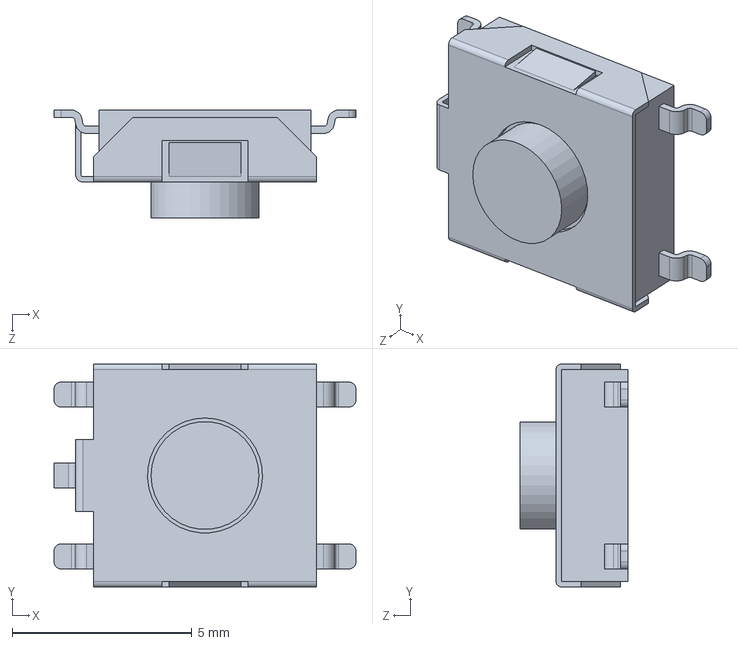
[picture p118: CAD file, 2022-09-26]
3D_Modelling/arduino-uno-r3/12. Button arduino.SLDPRT
8.40 x 6.20 x 3.00 mm
