swyou1123/ssokdam/3D_Modelling/Untact_Temp_Sensor.SLDPRT

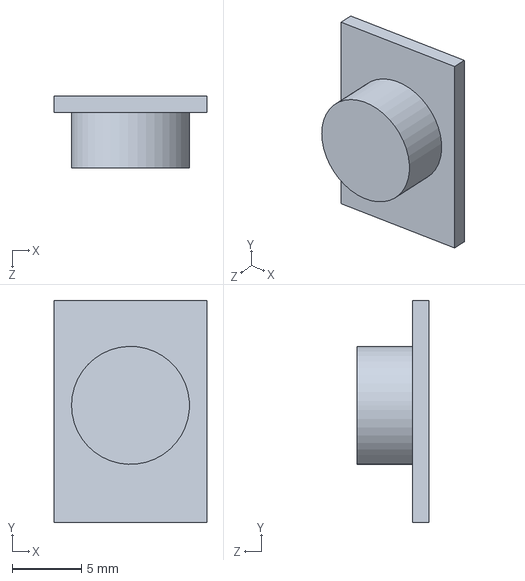
[picture p119: CAD file, 2022-09-26]
3D_Modelling/Untact_Temp_Sensor.SLDPRT
11.0 x 16.0 x 5.20 mm
