swyou1123/ssokdam/3D_Modelling/arduino-uno-r3/8. Arduino part 16MHZ.SLDPRT

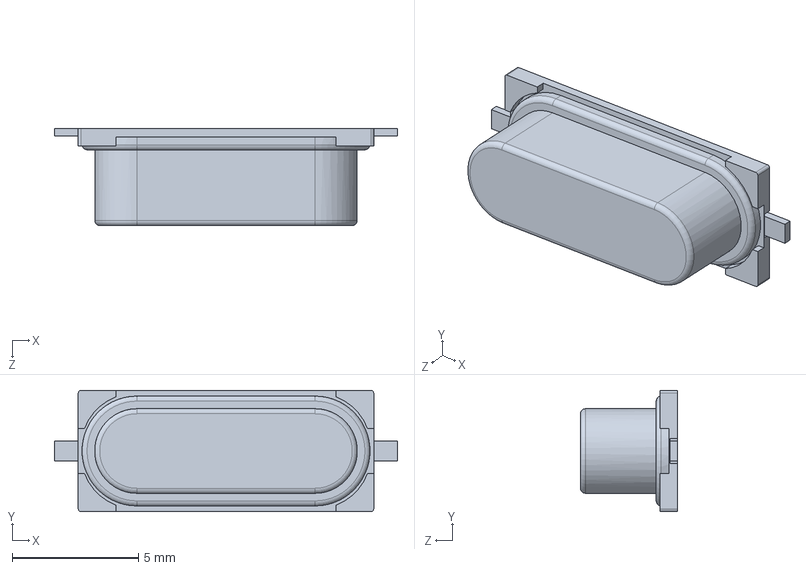
[picture p120: CAD file, 2022-09-26]
3D_Modelling/arduino-uno-r3/8. Arduino part 16MHZ.SLDPRT
13.6 x 4.80 x 3.85 mm
