swyou1123/ssokdam/3D_Modelling/Slider_1_Cover.SLDPRT

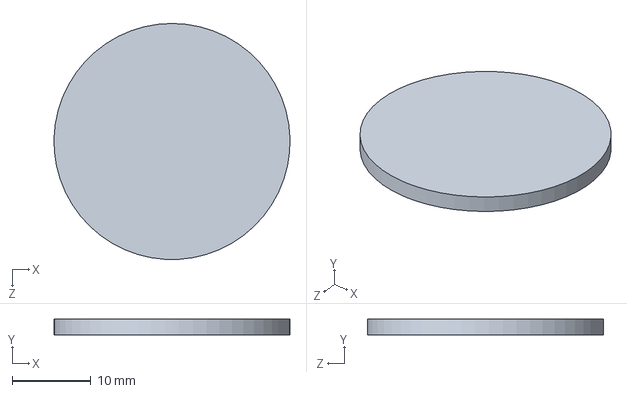
[picture p121: CAD file, 2022-09-26]
3D_Modelling/Slider_1_Cover.SLDPRT
30.0 x 2.00 x 30.0 mm
