swyou1123/ssokdam/3D_Modelling/arduino-uno-r3/14. Micro chip part Arduino.SLDPRT

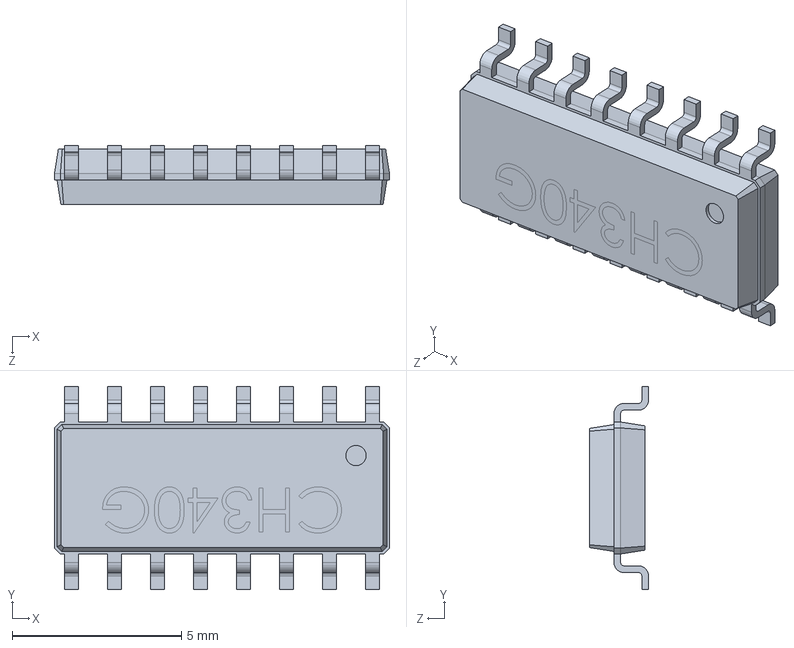
[picture p122: CAD file, 2022-09-26]
3D_Modelling/arduino-uno-r3/14. Micro chip part Arduino.SLDPRT
9.90 x 6.00 x 1.75 mm
