swyou1123/ssokdam/3D_Modelling/arduino-uno-r3/11. Transistor.SLDPRT

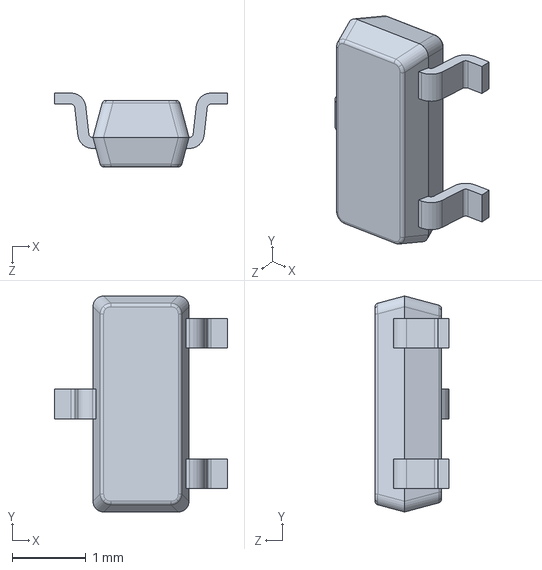
[picture p123: CAD file, 2022-09-26]
3D_Modelling/arduino-uno-r3/11. Transistor.SLDPRT
2.34 x 2.92 x 1.00 mm
