swyou1123/ssokdam/Embedded/STM32/NUCLEO-F446RE/Sensor/Loadcell/loadcell_3/Core/Inc/hx711.h

/*
 * hx711.h
 *
 *  Created on: Aug 1, 2022
 *      Author: multicampus
 */

#ifndef INC_HX711_H_
#define INC_HX711_H_

#include "stm32f4xx_hal.h"

typedef struct {
	GPIO_TypeDef* PD_SCK_PinType;	//GPIOx
	uint16_t PD_SCK_PinNumber;		//GPIO_Pin
	GPIO_TypeDef* DOUT_PinType;		//GPIOx
	uint16_t DOUT_PinNumber;		//GPIO_Pin
	int offset;
	float SCALE;
	int mode;		// 0 Input channel A, gain=128
					// 1 Input channel B, gain=32
					// 2 Input channel A, gain=64
} HX711;

int HX711_Read(HX711* H);
int HX711_AvgRead(HX711* H, int times);
void HX711_Tare(HX711* H, int times);
int HX711_GetValue(HX711* H);
int HX711_GetAvgValue(HX711* H, int times);



#endif /* INC_HX711_H_ */
