swyou1123/ssokdam/Embedded/STM32/NUCLEO-F446RE/Sensor/Loadcell/loadcell_3/Core/Src/hx711.c

/*
 * hx711.c
 *
 *  Created on: Aug 1, 2022
 *      Author: multicampus
 */


#include "hx711.h"

int HX711_Read(HX711* H) {
	int count = 0;
	_Bool isNegative = 0;
	HAL_GPIO_WritePin(H->PD_SCK_PinType, H->PD_SCK_PinNumber, GPIO_PIN_RESET);
	while (HAL_GPIO_ReadPin(H->DOUT_PinType, H->DOUT_PinNumber)) {

	}
	for (uint8_t i = 0; i < 24; i++) {
		HAL_GPIO_WritePin(H->PD_SCK_PinType, H->PD_SCK_PinNumber, GPIO_PIN_SET);
		count = count << 1;
		HAL_GPIO_WritePin(H->PD_SCK_PinType, H->PD_SCK_PinNumber,
				GPIO_PIN_RESET);
		if (HAL_GPIO_ReadPin(H->DOUT_PinType, H->DOUT_PinNumber)) {
			if (i == 0) {
				isNegative = 1;
			}
			count++;
		}
	}
	if (isNegative) {
		count = count ^ 0xFF000000;
	}
	HAL_GPIO_WritePin(H->PD_SCK_PinType, H->PD_SCK_PinNumber, GPIO_PIN_SET);
	HAL_GPIO_WritePin(H->PD_SCK_PinType, H->PD_SCK_PinNumber, GPIO_PIN_RESET);
	for (uint8_t i = 0; i < H->mode; i++) {
		HAL_GPIO_WritePin(H->PD_SCK_PinType, H->PD_SCK_PinNumber, GPIO_PIN_SET);
		HAL_GPIO_WritePin(H->PD_SCK_PinType, H->PD_SCK_PinNumber,
				GPIO_PIN_RESET);
	}
	return count;
}

int HX711_AvgRead(HX711* H, int times) {
	int sum = 0;
	for (uint8_t i = 0; i < times; i++) {
		sum += HX711_Read(H);
	}
	return sum / times;
}

void HX711_Tare(HX711* H, int times) {
	H->offset = HX711_AvgRead(H, times);
}

int HX711_GetValue(HX711* H) {
	return HX711_Read(H) - (H->offset);
}

int HX711_GetAvgValue(HX711* H, int times) {
	return HX711_AvgRead(H, times) - (H->offset);
}
